Hughger/graduate/accelerator/pics/MCU200T.JPG

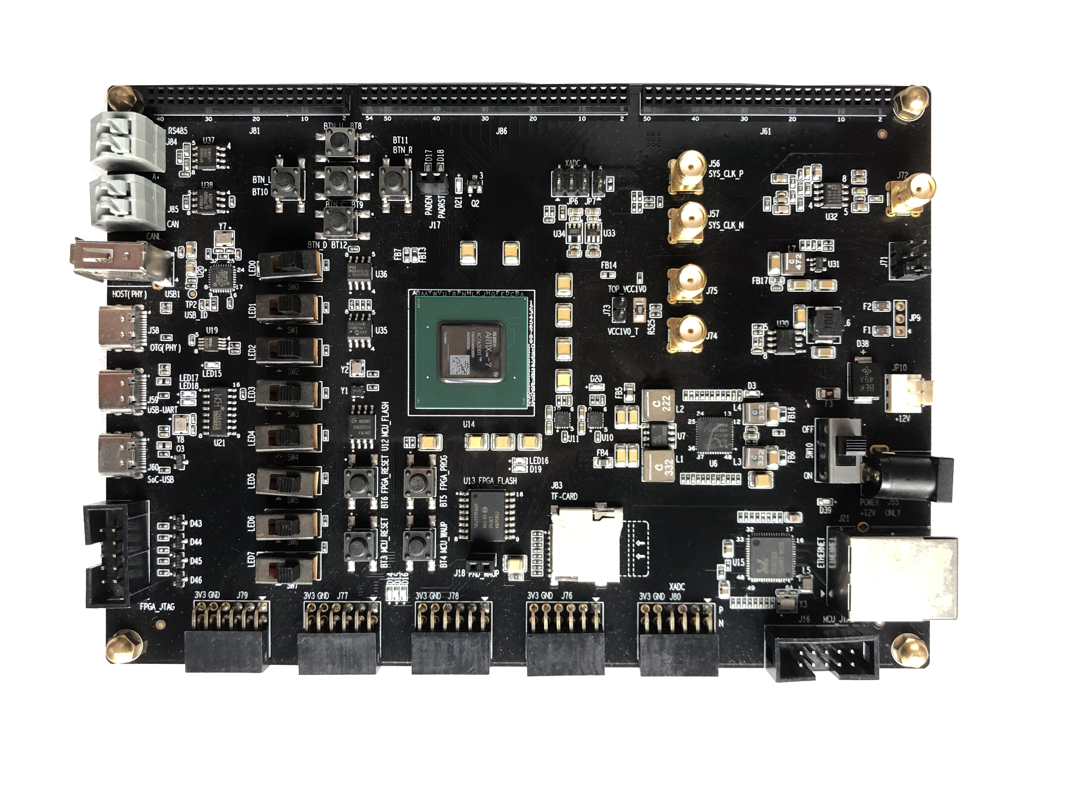
accelerator/pics/MCU200T.JPG
