Hughger/graduate/accelerator/note.md

# E203 RISC-V 处理器与 AHB 总线矩阵系统集成技术指南

## 目录
1.  [引言](#1-引言)
    1.1. [项目背景](#11-项目背景)
    1.2. [系统架构概述](#12-系统架构概述)
    1.3. [指南目标与范围](#13-指南目标与范围)
2.  [总线协议分析](#2-总线协议分析)
    2.1. [E203 内部 ICB 总线协议](#21-e203-内部-icb-总线协议)
        2.1.1. [ICB 总线信号详解](#211-icb-总线信号详解)
        2.1.2. [ICB 总线时序分析](#212-icb-总线时序分析)
    2.2. [AHB-Lite 与标准 AHB 协议](#22-ahb-lite-与标准-ahb-协议)
        2.2.1. [主要区别](#221-主要区别)
        2.2.2. [兼容性考量](#222-兼容性考量)
    2.3. [ICB 到 AHB-Lite 转换机制](#23-icb-到-ahb-lite-转换机制)
        2.3.1. [转换桥 (CIB2AHB) 的作用](#231-转换桥-cib2ahb-的作用)
        2.3.2. [信号匹配与转换逻辑](#232-信号匹配与转换逻辑)
        2.3.3. [被忽略或固定值的信号处理](#233-被忽略或固定值的信号处理)
3.  [代码级实现](#3-代码级实现)
    3.1. [关键源文件定位与修改](#31-关键源文件定位与修改)
        3.1.1. [E203 Core 相关文件](#311-e203-core-相关文件)
        3.1.2. [SoC 集成层面文件](#312-soc-集成层面文件)
        3.1.3. [总线矩阵配置文件](#313-总线矩阵配置文件)
    3.2. [地址空间分配](#32-地址空间分配)
        3.2.1. [系统地址映射规划](#321-系统地址映射规划)
        3.2.2. [E203 视角下的地址映射](#322-e203-视角下的地址映射)
        3.2.3. [修改地址译码逻辑](#323-修改地址译码逻辑)
    3.3. [在 AHB 矩阵中集成 E203 (作为主设备)](#33-在-ahb-矩阵中集成-e203-作为主设备)
        3.3.1. [AHB 主设备接口连接](#331-ahb-主设备接口连接)
        3.3.2. [总线矩阵仲裁配置](#332-总线矩阵仲裁配置)
    3.4. [AHB2APB 桥的连接与配置](#34-ahb2apb-桥的连接与配置)
        3.4.1. [APB 总线外设连接](#341-apb-总线外设连接)
        3.4.2. [配置寄存器访问 (regfile)](#342-配置寄存器访问-regfile)
    3.5. [最小化修改 E203 现有代码的策略](#35-最小化修改-e203-现有代码的策略)
4.  [集成挑战与解决方案](#4-集成挑战与解决方案)
    4.1. [多主设备环境下的总线仲裁](#41-多主设备环境下的总线仲裁)
    4.2. [地址映射与内存区域划分](#42-地址映射与内存区域划分)
    4.3. [数据宽度不匹配 (32位 E203 vs 64位 AHB/SRAM)](#43-数据宽度不匹配-32位-e203-vs-64位-ahbsram)
        4.3.1. [数据位宽转换逻辑](#431-数据位宽转换逻辑)
        4.3.2. [字节选通 (Byte Strobes) 处理](#432-字节选通-byte-strobes-处理)
    4.4. [时钟域同步](#44-时钟域同步)
        4.4.1. [CDC (Clock Domain Crossing) 设计](#441-cdc-clock-domain-crossing-设计)
        4.4.2. [异步 FIFO 的使用](#442-异步-fifo-的使用)
    4.5. [复位机制协调](#45-复位机制协调)
        4.5.1. [系统复位信号生成与分发](#451-系统复位信号生成与分发)
        4.5.2. [各模块复位序列](#452-各模块复位序列)
5.  [性能优化](#5-性能优化)
    5.1. [E203 访问内存的延迟分析与优化](#51-e203-访问内存的延迟分析与优化)
        5.1.1. [流水线与等待状态](#511-流水线与等待状态)
        5.1.2. [预取机制](#512-预取机制)
    5.2. [多主设备争用时的性能保障](#52-多主设备争用时的性能保障)
        5.2.1. [仲裁算法选择与调优](#521-仲裁算法选择与调优)
        5.2.2. [QoS (Quality of Service) 机制 (如果支持)](#522-qos-quality-of-service-机制-如果支持)
    5.3. [缓存策略调整建议 (E203 L1 Cache)](#53-缓存策略调整建议-e203-l1-cache)
6.  [调试与测试](#6-调试与测试)
    6.1. [总线信号监控点设置](#61-总线信号监控点设置)
        6.1.1. [关键信号列表](#611-关键信号列表)
        6.1.2. [ILA (Integrated Logic Analyzer) 使用](#612-ila-integrated-logic-analyzer-使用)
    6.2. [验证策略与测试用例设计](#62-验证策略与测试用例设计)
        6.2.1. [单元测试](#621-单元测试)
        6.2.2. [集成测试](#622-集成测试)
        6.2.3. [系统级测试](#623-系统级测试)
        6.2.4. [压力测试和边界条件测试](#624-压力测试和边界条件测试)
    6.3. [常见问题诊断与解决方法](#63-常见问题诊断与解决方法)
        6.3.1. [CPU 无法启动](#631-cpu-无法启动)
        6.3.2. [内存访问错误](#632-内存访问错误)
        6.3.3. [外设不工作](#633-外设不工作)
        6.3.4. [性能不达标](#634-性能不达标)
7.  [实现路线图](#7-实现路线图)
    7.1. [推荐的渐进式实现步骤](#71-推荐的渐进式实现步骤)
        7.1.1. [步骤一：基础 E203 系统搭建 (单主模式)](#711-步骤一基础-e203-系统搭建-单主模式)
        7.1.2. [步骤二：引入 AHB 总线矩阵和内存](#712-步骤二引入-ahb-总线矩阵和内存)
        7.1.3. [步骤三：集成 AHB2APB 桥和基础外设](#713-步骤三集成-ahb2apb-桥和基础外设)
        7.1.4. [步骤四：集成其他 AHB 主设备 (如 DMA, 网络接口)](#714-步骤四集成其他-ahb-主设备-如-dma-网络接口)
        7.1.5. [步骤五：集成 4x4 DSP 核心](#715-步骤五集成-4x4-dsp-核心)
    7.2. [关键验证点与里程碑](#72-关键验证点与里程碑)
    7.3. [最小可行产品 (MVP) 实现建议](#73-最小可行产品-mvp-实现建议)
8.  [附录](#8-附录)
    8.1. [相关术语解释](#81-相关术语解释)
    8.2. [参考资料](#82-参考资料)

## 1. 引言

### 1.1. 项目背景
随着物联网 (IoT)、嵌入式系统以及专用计算领域对高能效、可定制化处理器的需求日益增长，RISC-V 架构凭借其开放、模块化和可扩展的特性，受到了广泛关注。E203 是由芯来科技推出的一款基于 RISC-V RV32IMAC 指令集的低功耗、高性能嵌入式处理器核心。

在复杂的片上系统 (SoC) 设计中，处理器核心通常需要与多种内存、外设和加速器进行高效通信。AHB (Advanced High-performance Bus) 作为 AMBA (Advanced Microcontroller Bus Architecture) 总线规范的一部分，是连接这些组件的常用标准。本项目旨在将 E203 处理器集成到一个基于 AHB 总线矩阵的复杂系统中，该系统包含 DDR/SRAM 内存、网络接口、DMA 控制器以及一个专用的 4x4 DSP 计算核心，以满足特定应用场景下的数据处理和控制需求。

本指南将详细阐述集成过程中涉及的关键技术环节，旨在为初次接触此类项目的工程师提供清晰、详尽的操作指引。

### 1.2. 系统架构概述
根据提供的系统框图，我们集成的目标系统主要包含以下关键模块：

*   **E203 RISC-V 处理器**：作为系统的核心控制器，负责执行主程序逻辑。E203 处理器通过其内部的 ICB (Instruction and Data Coherent Bus) 总线（32位）与外界交互。
*   **CIB2AHB (ICB to AHB Bridge)**：这是一个关键的桥接模块，负责将 E203 的 32位 ICB 总线协议转换为 AHB-Lite 总线协议，使其能够连接到 AHB 总线矩阵。
*   **AHB 总线矩阵 (AHB Matrix)**：作为系统数据交换的枢纽，连接了多个主设备 (Master) 和从设备 (Slave)。
    *   **主设备 (Masters)** 包括：
        *   E203 处理器 (通过 CIB2AHB，32位接口)
        *   三个 DMA 控制器 (DMA0, DMA1, DMA2，预计为64位接口)
        *   网络接口或其他高速外设 (预计为64位接口)
    *   **从设备 (Slaves)** 包括：
        *   DDR/SRAM 内存控制器 (64位接口)
        *   AHB2APB 桥 (为 E203 提供访问低速外设的通道，如配置寄存器)
        *   DMA 控制器的从接口 (用于接收来自 AHB Matrix 的数据传输指令或状态查询)
*   **DDR/SRAM 内存**：系统主内存，通过 64位接口连接到 AHB 总线矩阵，供 E203 和其他主设备访问。
*   **网络接口/其他外设**：作为 AHB 主设备，通过 64位接口与系统其他部分进行数据交换。
*   **4x4 DSP 核心**：专用的数字信号处理单元，不直接挂载在 AHB 总线矩阵上。它通过三个专用的 SRAM (sram0 用于输入，sram1 用于权重，sram2 用于输出) 与系统交互。
    *   DMA0 负责将输入数据从系统内存（如 DDR/SRAM）搬运到 `sram0` (64位 -> 512位路径)。
    *   DMA1 负责将权重数据搬运到 `sram1` (64位 -> 512位路径)。
    *   `sram0` 和 `sram1` 的数据提供给 4x4 DSP 核心进行计算。
    *   DSP 核心的计算结果存入 `sram2` (512位)。
    *   DMA2 负责将 `sram2` 中的输出数据搬运回系统内存 (512位 -> 64位路径)。
*   **AHB2APB 桥 (AHB to APB Bridge)**：连接到 AHB 总线矩阵，并将 AHB 事务转换为 APB (Advanced Peripheral Bus) 事务。APB 总线通常用于连接低带宽、低功耗的外设，如本系统中的**配置寄存器**。E203 通过此桥来配置和控制这些外设。
*   **数据位宽**：系统存在多种数据位宽：
    *   E203 CPU 核及 CIB2AHB 输出为 32 位。
    *   AHB 矩阵的大部分高速接口（DDR/SRAM, DMA, 网络接口）为 64 位。
    *   DSP 核相关的 SRAM 接口为 512 位。
    *   AHB2APB 桥的 AHB 侧通常与 CPU 位宽匹配 (32位)，APB 侧位宽根据外设需求而定。

理解这些模块及其交互方式是成功集成的第一步。

### 1.3. 指南目标与范围
本指南的目标是为用户提供一个全面、细致的集成方案，涵盖从理论分析到具体实践的各个方面。主要内容包括：

*   **深入的总线协议理解**：解析 E203 的 ICB 总线、AHB-Lite 与标准 AHB 的差异，以及 ICB 到 AHB-Lite 的转换细节。
*   **详细的代码级实现指导**：指出需要修改的关键源文件、地址空间的配置方法、E203 在 AHB 矩阵中的集成方式以及 AHB2APB 桥的连接。
*   **清晰的集成挑战剖析**：讨论多主仲裁、地址映射、数据宽度不匹配、时钟域同步和复位协调等常见难题及应对策略。
*   **实用的性能优化建议**：针对内存访问延迟、总线争用和缓存利用提出优化方案。
*   **系统的调试与测试方法**：提供总线监控、验证策略和问题排查的思路。
*   **明确的实现路线图**：给出分步实施计划、关键验证节点和 MVP (Minimum Viable Product) 建议。

本指南力求做到：
*   **逻辑清晰**：确保内容的组织结构合理，易于理解。
*   **深度与形象并存**：在保证技术深度的同时，采用生动的描述和必要的图示（尽管本文档主要为文本）来帮助理解。
*   **细节充分**：提供足够的代码示例（概念性或通用性）、配置参数和修改建议。

**范围限制**：
*   本指南主要关注 E203 处理器与 AHB 总线系统的集成。对于特定外设（如 DDR 控制器、网络接口、DSP 核）的内部详细设计和驱动开发，将不作深入探讨，仅涉及其与总线接口相关的部分。
*   提供的代码示例将主要基于通用 Verilog/SystemVerilog 描述，具体实现可能需要根据用户实际使用的 E203 版本和 SoC 开发环境进行调整。
*   本指南假设用户具备基础的数字逻辑设计、Verilog/SystemVerilog 语言以及嵌入式系统概念的知识。

希望通过本指南，即使是刚接触此项目的工程师也能对集成过程有一个清晰的认识，并能够按部就班地完成各项任务。

## 2. 总线协议分析

理解系统中涉及的各种总线协议是成功集成的基石。本章节将重点分析 E203 处理器的内部总线 (ICB)、目标系统总线 (AHB-Lite/AHB) 以及它们之间的转换机制。

### 2.1. E203 内部 ICB 总线协议
E203 处理器核（如本项目中的 e203_hbirdv2）使用一种称为 ICB (Internal Chip Bus) 的内部总线接口。这是一种同步总线协议，用于连接处理器核的指令获取单元 (IFU) 和加载存储单元 (LSU) 到外部总线桥 (如 CIB2AHB，连接到 AHB 系统总线) 或紧耦合内存 (TCM)。ICB 通常具有分离的命令和响应通道，并使用 `valid/ready` 握手机制。

该项目的 RTL 代码中，通过 `rtl/e203/core/e203_ifu_ift2icb.v` 文件可以了解到 IFU 侧的 ICB 接口信号，通过 `rtl/e203/core/e203_lsu.v`、`rtl/e203/core/e203_biu.v` 等文件可以明确 LSU 侧的 ICB 接口信号。相关信号的位宽则由 `rtl/e203/core/e203_defines.v` (及其包含的 `config.v`) 文件确定。

#### 2.1.1. ICB 总线信号详解
E203 的 ICB 接口分为指令端 (IFU) 和数据端 (LSU)。以下是基于对 `e203_hbirdv2` RTL 核心代码的分析所确认的信号描述。

**通用 ICB 信号特性:**
*   所有 ICB 信号均同步于处理器的核心时钟。
*   使用 `valid/ready` 握手协议。
*   命令通道 (`_cmd_`) 和响应通道 (`_rsp_`) 通常是分离的。

**1. 指令获取单元 (IFU) 的 ICB 主接口 (例如，连接到 BIU 的前缀为 `ifu2biu_icb_`，连接到 ITCM 的前缀为 `ifu2itcm_icb_`)**
   IFU 主要发起读请求以获取指令，因此其 ICB 接口主要涉及读操作。

*   **请求通道 (IFU -> BIU/ITCM)**
    *   `ifu_icb_cmd_valid`: 1位输出，命令有效。表示 IFU 发出一个有效的指令读取请求。
    *   `ifu_icb_cmd_addr`: [`E203_ADDR_SIZE-1:0`] 输出，请求的指令地址。位宽由 `E203_ADDR_SIZE` (例如32位) 决定。
    *   `ifu_icb_cmd_read`: 1位输出，恒为1，表示读请求。(在 `e203_biu.v` 中，`ifu2biu_icb_cmd_read` 信号存在且被使用)
    *   `ifu_icb_cmd_burst`: 2位输出 (例如在 `ifu2biu_icb_cmd_burst`)，突发类型 (如 `INC4`, `SINGLE`)。
    *   `ifu_icb_cmd_beat`: 2位输出 (例如在 `ifu2biu_icb_cmd_beat`)，突发拍数。
    *   `ifu_icb_cmd_lock`: 1位输出 (例如在 `ifu2biu_icb_cmd_lock`)，指示锁定传输 (通常对 IFU 为低)。
    *   `ifu_icb_cmd_excl`: 1位输出 (例如在 `ifu2biu_icb_cmd_excl`)，指示独占访问 (通常对 IFU 为低)。
    *   `ifu_icb_cmd_size`: 2位输出 (例如在 `ifu2biu_icb_cmd_size`)，传输大小 (例如字节、半字、字)。

*   **命令响应通道 (BIU/ITCM -> IFU)**
    *   `ifu_icb_cmd_ready`: 1位输入，命令准备好。表示总线桥或 ITCM 可以接收 IFU 的新请求。

*   **读数据响应通道 (BIU/ITCM -> IFU)**
    *   `ifu_icb_rsp_valid`: 1位输入，响应有效。表示总线桥或 ITCM 返回了有效的指令数据或错误指示。
    *   `ifu_icb_rsp_rdata`: [`E203_SYSMEM_DATA_WIDTH-1:0`] 或 [`E203_ITCM_DATA_WIDTH-1:0`] 输入，读取到的指令数据。位宽取决于目标：
        *   系统内存 (BIU): `E203_SYSMEM_DATA_WIDTH` (例如32位或64位)。
        *   ITCM: `E203_ITCM_DATA_WIDTH` (例如64位)。
    *   `ifu_icb_rsp_err`: 1位输入，响应错误。表示指令读取过程中发生错误。
    *   `ifu_icb_rsp_excl_ok`: 1位输入 (例如在 `ifu2biu_icb_rsp_excl_ok`)，独占访问成功 (通常对 IFU 为低)。
    *   `ifu_icb_rsp_ready`: 1位输出，响应准备好。表示 IFU 可以接收响应数据/错误。

**2. 加载存储单元 (LSU) 的 ICB 主接口 (例如，连接到 BIU 的前缀为 `lsu2biu_icb_`，连接到 DTCM 的前缀为 `lsu2dtcm_icb_`)**
   LSU 发起读写请求以访问数据内存。其信号集比 IFU 更完整，支持写操作、字节使能、独占访问等。

*   **请求通道 (LSU -> BIU/DTCM)**
    *   `lsu_icb_cmd_valid`: 1位输出，命令有效。
    *   `lsu_icb_cmd_addr`: [`E203_ADDR_SIZE-1:0`] 输出，访问地址。
    *   `lsu_icb_cmd_read`: 1位输出，读写指示。高电平表示读，低电平表示写。
    *   `lsu_icb_cmd_wdata`: [`E203_XLEN-1:0`] 输出，写数据。CPU 内核数据宽度 `E203_XLEN` 通常为32位。
    *   `lsu_icb_cmd_wmask`: [`E203_XLEN/8-1:0`] 输出，写操作字节使能。对于32位 `E203_XLEN`，此宽度为4位 (例如 `0b0001` 写低字节, `0b1111` 写整个字)。
    *   `lsu_icb_cmd_lock`: 1位输出，锁定传输信号。用于原子操作或连续不可中断的访问。
    *   `lsu_icb_cmd_excl`: 1位输出，独占访问请求。用于 Load-Reserved/Store-Conditional (LR/SC) 指令。
    *   `lsu_icb_cmd_size`: 2位输出，传输大小。编码方式通常为 `00`: 字节, `01`: 半字, `10`: 字。
    *   `lsu_icb_cmd_burst`: (可选，但在 `lsu2biu_icb_` 接口中存在) 2位输出，突发类型。
    *   `lsu_icb_cmd_beat`: (可选，但在 `lsu2biu_icb_` 接口中存在) 2位输出，突发拍数。
    *   `lsu_icb_cmd_amo`: RISC-V 'A' 扩展中的原子内存操作并非通过一个名为 `lsu_icb_cmd_amo` 的专用多位ICB信号直接指示其类型。其功能主要通过 `lsu_icb_cmd_excl` (用于LR/SC) 和常规的读写操作，结合LSU内部逻辑 (如 `e203_lsu.v` 中的 `lsu_req_amo` 信号输入给LSU控制逻辑) 来实现。

*   **命令响应通道 (BIU/DTCM -> LSU)**
    *   `lsu_icb_cmd_ready`: 1位输入，命令准备好。

*   **读数据/写响应通道 (BIU/DTCM -> LSU)**
    *   `lsu_icb_rsp_valid`: 1位输入，响应有效。
    *   `lsu_icb_rsp_rdata`: [`E203_SYSMEM_DATA_WIDTH-1:0`] 或 [`E203_DTCM_DATA_WIDTH-1:0`] 输入，读数据。位宽取决于目标：
        *   系统内存 (BIU): `E203_SYSMEM_DATA_WIDTH` (例如32位或64位)。
        *   DTCM: `E203_DTCM_DATA_WIDTH` (例如32位)。
    *   `lsu_icb_rsp_err`: 1位输入，响应错误。例如，总线错误 (slave error) 或独占访问失败。
    *   `lsu_icb_rsp_excl_ok`: 1位输入，独占访问成功响应。对于 SC 指令，此信号高表示原子写操作成功。
    *   `lsu_icb_rsp_ready`: 1位输出，响应准备好。LSU 准备好接收读数据或写响应。

**关键特性总结 (基于对 `e203_hbirdv2` RTL 的分析):**
*   **分离的指令和数据接口**: E203 核的 IFU 和 LSU 分别通过独立的 ICB 接口连接到总线接口单元 (BIU) 或直接连接到 TCM。BIU 内部会将这些请求仲裁并转发到外部总线 (如 AHB)。
*   **握手协议**: `valid/ready` 机制确保命令和响应的可靠传输。
*   **支持原子操作**: LSU 的 ICB 接口通过 `_cmd_excl` 和 `_rsp_excl_ok` 支持 RISC-V 的 Load-Reserved/Store-Conditional (LR/SC) 指令，这是实现原子操作的基础。对于其他的 AMO 指令 (如 AMOSWAP, AMOADD 等)，LSU 内部 (`e203_exu_alu_lsuagu.v` 解码生成 `agu_i_amo*` 信号, 传递给 `e203_lsu.v` 的 `lsu_req_amo*` 输入) 会将这些操作分解为一个或多个 ICB 读和/或写事务，配合 `_cmd_lock` (如果需要确保操作的原子性不被外部总线仲裁打断) 或 `_cmd_excl` (对于 LR/SC 序列) 来完成。LSU 对外的 ICB 接口上并没有一个专门的 `lsu_icb_cmd_amo` 多位信号来直接传递 AMO 操作的类型。
*   **支持不同传输大小**: `_cmd_size` 信号允许字节、半字和字访问。
*   **突发传输能力**: IFU 和 LSU 到 BIU 的 ICB 接口均包含 `_cmd_burst` 和 `_cmd_beat` 信号，表明 ICB 支持突发传输，这对于提高数据传输效率非常重要。

#### 2.1.2. ICB 总线时序分析
ICB 总线是一种同步总线，所有信号都相对于同一个时钟沿进行采样和驱动。

*   **读操作时序 (简例，以LSU为例)**：
    1.  **T1周期**：LSU 主设备拉高 `lsu_icb_cmd_valid`，并驱动 `lsu_icb_cmd_addr` (读地址) 和 `lsu_icb_cmd_read` (高电平)。
    2.  总线桥/从设备在同一周期或稍后周期拉高 `lsu_icb_cmd_ready` (如果能立即接收)。命令被锁存。
    3.  经过若干周期（取决于从设备延迟），总线桥/从设备准备好读数据。
    4.  **Tn周期**：总线桥/从设备拉高 `lsu_icb_rsp_valid`，并驱动 `lsu_icb_rsp_rdata` (读出的数据) 和 `lsu_icb_rsp_err` (若有错误)。LSU 此时拉高 `lsu_icb_rsp_ready` (通常 LSU 会一直拉高 `rsp_ready` 表示能接收) 接收响应。

*   **写操作时序 (简例，以LSU为例)**：
    1.  **T1周期**：LSU 主设备拉高 `lsu_icb_cmd_valid`，并驱动 `lsu_icb_cmd_addr` (写地址)，`lsu_icb_cmd_read` (低电平)，`lsu_icb_cmd_wdata` (写数据) 和 `lsu_icb_cmd_wmask`。
    2.  总线桥/从设备在同一周期或稍后周期拉高 `lsu_icb_cmd_ready`。命令和数据被锁存。
    3.  经过若干周期，写操作完成。
    4.  **Tm周期**：总线桥/从设备拉高 `lsu_icb_rsp_valid` (指示写完成) 和 `lsu_icb_rsp_err` (若有错误)。LSU 接收写响应。

**关键时序考量**：
*   **延迟 (Latency)**：从命令发出到接收到响应（读数据或写完成）的时钟周期数。
*   **吞吐率 (Throughput)**：单位时间内可以传输的数据量。ICB 的设计允许一定程度的流水线操作，即在等待前一个命令的响应时，可以发出新的命令 (如果 `icb_cmd_ready` 允许)。

### 2.2. AHB-Lite 与标准 AHB 协议
AMBA AHB (Advanced High-performance Bus) 是一种广泛使用的高性能片上总线协议。AHB-Lite 是 AHB 的一个子集，专为单个主设备系统或不需复杂仲裁和不支持分离事务的场景设计，但它也可以作为多主系统中连接简单主设备或通过桥接转换后的主设备接口。

#### 2.2.1. 主要区别
下表总结了 AHB-Lite 与标准 AHB (例如 AHB5，但也适用于早期版本如 AHB2) 的一些主要区别：

| 特性 | 标准 AHB (Full AHB) | AHB-Lite |
| --- | --- | --- |
| **主设备数量** | 支持多个主设备 (Multi-Master) | 通常用于单个主设备，或多主系统中简单主设备接口 |
| **仲裁** | 需要中央仲裁器 (Arbiter) | 无内置仲裁逻辑 (假定只有一个主设备，或由外部处理) |
| **分离事务** | 支持 (Split Transactions) | 不支持 |
| **流水线深度** | 通常支持更深的流水线 | 流水线相对简单 |
| **RETRY响应** | 支持 | 不支持 (通常 slave 用 HREADY 拉长传输) |
| **保护信号** | `HPROT` 提供更丰富的保护信息 | `HPROT` 可能被简化或固定 |
| **锁定传输** | `HLOCKx` 支持精确的锁定序列 | `HLOCKx` 通常用于简单的锁定传输 |
| **突发操作** | 支持多种复杂的突发类型 (e.g., WRAP4/8/16, INCR4/8/16) | 支持基本的 INCR 和 SINGLE 突发类型 |
| **信号数量** | 信号较多 | 信号较少 |

在我们的系统中，E203 通过 CIB2AHB 桥连接到 AHB 总线矩阵。这意味着 CIB2AHB 模块的输出是 AHB-Lite 兼容的接口，而 AHB 总线矩阵本身则需要处理来自多个主设备（包括转换后的 E203）的请求，因此总线矩阵必须实现仲裁逻辑，表现得像一个标准 AHB 系统中的互联结构。

#### 2.2.2. 兼容性考量
*   **AHB-Lite 主设备到标准 AHB 从设备**：通常是兼容的。AHB-Lite 主设备发出的事务可以被标准 AHB 从设备理解和处理。从设备通过 `HREADY` 信号来控制传输的完成，通过 `HRESP` 来指示成功或错误。
*   **AHB-Lite 主设备到 AHB 总线矩阵**：CIB2AHB 产生的 AHB-Lite 信号作为主设备接口连接到 AHB 总线矩阵的一个主端口。总线矩阵负责将来自 E203 (以及其他主设备) 的请求路由到相应的从设备，并处理仲裁。
*   **关键信号**：对于 AHB-Lite 主设备，核心信号包括：
    *   `HCLK`: 总线时钟
    *   `HRESETn`: 总线复位 (低有效)
    *   `HADDR[31:0]`: 地址总线
    *   `HWDATA[31:0]`: 写数据总线 (对于32位系统)
    *   `HRDATA[31:0]`: 读数据总线 (对于32位系统)
    *   `HWRITE`: 传输方向 (高=写, 低=读)
    *   `HSIZE[2:0]`: 传输大小 (字节,半字,字)
    *   `HBURST[2:0]`: 突发类型 (SINGLE, INCR, WRAP4, INCR4, etc.)
    *   `HPROT[3:0]`: 保护控制 (指令/数据, 用户/特权, 可缓冲, 可缓存)
    *   `HTRANS[1:0]`: 传输类型 (IDLE, BUSY, NONSEQ, SEQ)
    *   `HMASTLOCK`: 主设备锁定总线
    *   `HSELx`: 从设备选择信号 (由总线矩阵或地址译码器产生，送给从设备)
    *   `HREADY`: 从设备或总线准备好信号 (输入到主设备)。高表示传输完成，低表示等待。
    *   `HRESP`: 从设备响应 (OKAY, ERROR)

### 2.3. ICB 到 AHB-Lite 转换机制
CIB2AHB (ICB to AHB Bridge) 模块是实现 E203 处理器与 AHB 总线系统对接的关键。它扮演着协议转换器的角色。

#### 2.3.1. 转换桥 (CIB2AHB) 的作用
CIB2AHB 模块的主要职责是将 E203 CPU 核发出的 ICB 总线事务（读/写请求）转换为标准的 AHB-Lite 总线事务，并将 AHB 从设备返回的响应（读数据、错误状态）转换回 ICB 总线的响应格式。

具体功能包括：
1.  **地址和控制信号映射**：将 ICB 的地址、读写控制、字节使能等信号转换为 AHB 的 `HADDR`, `HWRITE`, `HSIZE`, `HWDATA` (部分字节由 `icb_cmd_wmask` 控制) 等。
2.  **时序匹配**：ICB 通常是 `valid/ready` 握手，AHB 也有其两阶段（地址相、数据相）和 `HREADY` 控制的握手机制。桥需要正确处理这些时序关系。
3.  **响应转换**：将 AHB 的 `HRDATA`, `HRESP` 转换为 ICB 的 `icb_rsp_rdata`, `icb_rsp_err`。
4.  **错误处理**：将 AHB 总线错误 (`HRESP`=ERROR) 传递回 ICB 总线。
5.  **等待状态插入**：如果 AHB 从设备通过拉低 `HREADY` 来请求等待状态，CIB2AHB 桥需要相应地暂停对 E203 ICB 总线的 `icb_cmd_ready` (如果 CPU 正在等待上一个命令完成才能发下一个) 或/和 `icb_rsp_valid`。

#### 2.3.2. 信号匹配与转换逻辑 (示例性，基于更新的 ICB 信号知识)
以下是一些典型的信号映射关系 (重点关注 LSU 的 D-ICB，因为它更完整):

*   **ICB Command (CPU LSU -> Bridge) to AHB (Bridge -> Matrix/Slave)**:
    *   `lsu_icb_cmd_addr`[`E203_ADDR_SIZE-1:0`] -> `HADDR`[`E203_ADDR_SIZE-1:0`] (或根据系统AHB总线宽度调整，通常CPU地址总线宽度与AHB地址总线宽度一致，均为32位)
    *   `lsu_icb_cmd_read` (1 for read, 0 for write) -> `HWRITE` (0 for read, 1 for write) (注意逻辑反转)
    *   `lsu_icb_cmd_wdata`[`E203_XLEN-1:0`] -> `HWDATA`[`E203_XLEN-1:0`] (在写操作时，通常 E203_XLEN 是32位，对应32位 AHB 数据总线)
    *   `lsu_icb_cmd_wmask`[`E203_XLEN/8-1:0`] -> 转换为 AHB 的 `HSIZE`。AHB-Lite 本身不直接使用字节选通信号 `HSTRB` (那是 AXI 的特性)。`HSIZE` 结合地址的低两位来确定传输的字节、半字或字。CIB2AHB 桥需要根据 `lsu_icb_cmd_wmask` 和 `lsu_icb_cmd_addr`的低位来生成正确的 `HSIZE` 和 `HADDR`。例如：
        *   写字节 (e.g., `4'b0001` at addr `0x0`): `HSIZE=000` (byte), `HADDR[1:0]=00`
        *   写半字 (e.g., `4'b0011` at addr `0x0`): `HSIZE=001` (halfword), `HADDR[1:0]=00`
        *   写字 (e.g., `4'b1111` at addr `0x0`): `HSIZE=010` (word), `HADDR[1:0]=00`
        如果 ICB 发出的是对齐的32位访问 (`wmask=4'b1111`)，则 `HSIZE` 通常设为 `3'b010` (32-bit word)。对于部分写 (如 `sb`, `sh`)，桥需要正确设置 `HSIZE` 并确保 `HADDR` 对齐到 `HSIZE` 的边界，同时 `HWDATA` 中只有对应的字节/半字数据是有效的（其他字节可以是不定值，从设备应忽略）。
    *   `lsu_icb_cmd_valid` -> 触发 AHB 传输的开始 (`HTRANS` 从 IDLE 变为 NONSEQ/SEQ)。
    *   `lsu_icb_cmd_ready` (from Bridge to CPU) -> 当桥的 AHB 侧可以发起新传输或已完成当前传输的地址阶段时，可以拉高 `lsu_icb_cmd_ready`。

*   **AHB Response (Matrix/Slave -> Bridge) to ICB Response (Bridge -> CPU LSU)**:
    *   `HRDATA`[`E203_XLEN-1:0`] (假设AHB数据总线与CPU XLEN一致) -> `lsu_icb_rsp_rdata`[`E203_XLEN-1:0`] (在读操作响应时)
    *   `HRESP` (OKAY/ERROR) -> `lsu_icb_rsp_err` (ERROR 时 `lsu_icb_rsp_err` 为高)
    *   `HREADY` (high indicates data phase completion) -> 触发 `lsu_icb_rsp_valid` 的产生。

**事务状态机**: CIB2AHB 内部会有一个状态机来管理 ICB 请求到 AHB 事务的转换过程，包括 AHB 的地址阶段和数据阶段，以及处理 `HREADY` 引入的等待周期。

**突发传输 (Burst)**：
*   如果 ICB 接口 (`lsu_icb_cmd_burst`, `lsu_icb_cmd_beat`) 支持突发，CIB2AHB 桥需要将这些转换为 AHB 的 `HBURST` 和管理多拍 (`HTRANS` 为 SEQ)。
*   如果 E203 配置了指令缓存 (I-Cache) 或数据缓存 (D-Cache)（通过如 `E203_HAS_ICACHE`/`E203_HAS_DCACHE` 等宏配置），其缓存行（Cache line）的填充 (fill) 或写回 (write-back) 操作会在 ICB 层面产生突发请求，利用 `ifu2biu_icb_cmd_burst`/`beat` 或 `lsu2biu_icb_cmd_burst`/`beat` 信号。标准的 RISC-V 指令集不包含 LDM/STM (加载/存储多寄存器) 指令，E203 的公开资料和代码中也未明确提及此类自定义指令。
*   如果 ICB 不直接支持突发，但 CPU 连续发出地址相邻的请求，桥也可以选择将它们合并成一个 AHB 突发（需要更复杂的逻辑）。更常见的是，CPU的加载/存储多寄存器指令或 Cache 操作会触发桥产生固定长度的 AHB 突发。

#### 2.3.3. 被忽略或固定值的信号处理
在 ICB 到 AHB-Lite 的转换中，某些 AHB 信号可能对于简单的 E203 应用场景不是必需的，或者其值可以固定：

*   **`HMASTLOCK`**: 如果 E203 的 `lsu_icb_cmd_lock` 被驱动，则桥应相应驱动 `HMASTLOCK`。
*   **`HPROT` (Protection Control)**: ICB 的 `lsu_icb_cmd_prot` (如果存在) 可以部分映射到 `HPROT`。CIB2AHB 需要根据 E203 的内存访问类型（指令取指、数据加载/存储，通过是I-ICB还是D-ICB判断）以及当前的运行模式（用户态/特权态，这部分信息需要 CIB2AHB 桥根据 E203 的当前状态和访问特性来生成。具体来说：CPU 的当前特权级别（用户态/机器态，可从 CSR如 `mstatus` 获取）会影响 `HPROT[1]` (user/privilege)；访问的内存区域属性（是否可缓存、可缓冲，由 PMP 单元或地址区域的默认设定决定）会影响 `HPROT[3]` (cacheable) 和 `HPROT[2]` (bufferable)；访问是取指还是数据访问会影响 `HPROT[0]` (instruction/data)。PMP 单元会检查访问权限，但具体的属性信息（用于 `HPROT\`）如何从 PMP 传递给桥，取决于桥和 PMP 的接口设计，或桥通过地址范围和操作类型推断。)来设置这些位。
*   **`HBURST`**: 根据 `lsu_icb_cmd_burst` (如果存在) 或固定为 SINGLE/INCR。
*   **`HSIZE`**: 根据 `lsu_icb_cmd_wmask` 和地址低位计算，或对于IFU固定为适合指令获取的宽度（通常是字）。

理解这些协议细节和转换机制，对于后续的 RTL 代码修改、地址映射配置以及系统调试至关重要。

## 3. 代码级实现

本章节将指导您如何在 RTL (Register Transfer Level) 代码层面进行 E203 处理器与 AHB 总线矩阵系统的集成。这通常涉及到修改现有的 SoC 顶层文件、总线桥接逻辑、以及可能的处理器配置。

**重要提示**：以下提供的路径和文件名是基于典型 E203 项目结构和通用 SoC 设计实践的推测。您需要根据您项目中 `e203_hbirdv2` 代码库的实际结构来定位和修改相应文件。

### 3.1. 关键源文件定位与修改

#### 3.1.1. E203 Core 相关文件
*   **确切路径**: `rtl/e203/core/` （本项目已确认）
*   **关注点**: 通常情况下，E203 处理器核本身（如 `e203_cpu_top.v` 或类似文件）的 ICB 接口是标准化的，**不建议直接修改处理器核内部代码**，除非有非常特殊且明确的需求（例如，调整内部 TCM 大小或接口特性，但这通常通过顶层参数配置实现）。
*   **主要操作**: 理解 E203 核的 ICB 主端口（指令和数据）的信号列表和时序特性。这些信息通常在处理器核的顶层模块定义中可以找到，或者在其相关的接口定义文件（如 `e203_defines.v` 或 `e203_icb_if.vh` 等，如果存在的话）。

#### 3.1.2. CIB2AHB (ICB to AHB Bridge) 模块
*   **确切文件**: `rtl/e203/general/sirv_gnrl_icbs.v` 中的模块 `sirv_gnrl_icb2ahbl`（行号 1467 起）。该模块已完整实现 32-bit ICB → AHB-Lite 转换，无需再编写新桥。
*   **关注点**: 这是集成的核心模块之一。
    *   **参数配置**: 检查该桥模块是否有可配置的参数，例如 AHB 数据位宽（虽然图示中 E203 侧是32位，但桥的 AHB 输出也是32位）、地址位宽、是否支持某些 AHB 特性（如锁定传输）。
    *   **ICB 接口连接**: 确保 E203 处理器的指令 ICB (I-ICB) 和数据 ICB (D-ICB) 正确连接到此桥的对应 ICB 从端口。
        *   E203 通常有独立的指令获取接口和数据访问接口。这两个接口可能连接到同一个 CIB2AHB 模块（如果桥内部有仲裁能力和端口合并），或者分别连接到不同的总线路径或桥模块。根据系统图，E203 通过一个 CIB2AHB 连接到 AHB Matrix，这意味着指令和数据请求都通过这个桥。
    *   **AHB 主接口信号**: 桥模块输出的 AHB 主接口信号（`HADDR`, `HWDATA`, `HWRITE`, `HTRANS`, `HSIZE`, `HBURST`, `HPROT`, `HMASTLOCK` 等）需要被引出，并连接到 AHB 总线矩阵的主端口。
    *   **AHB 从响应信号**: 从 AHB 总线矩阵返回的响应信号（`HRDATA`, `HREADYIN` (来自被选中从设备的HREADY), `HRESP`）需要正确输入到桥模块。
*   **修改示例 (概念性 Verilog 片段 - 模块实例化)**:
    ```verilog
    // 在 SoC 顶层或子系统中实例化 CIB2AHB 桥
    // (假设 E203 的指令和数据 ICB 合并或通过同一桥访问)
    wire [31:0] e203_icb_cmd_addr;
    wire        e203_icb_cmd_valid;
    // ... 其他 E203 ICB 信号 ...
    wire [31:0] ahb_master_haddr;
    wire        ahb_master_hwrite;
    // ... 其他桥输出的 AHB 主接口信号 ...
    wire [31:0] ahb_slave_hrdata;
    wire        ahb_slave_hready;
    // ... 其他桥输入的 AHB 从响应信号 ...

    cib2ahb_bridge_wrapper u_cib2ahb_bridge (
        // ICB Slave Interface (Connected to E203 Master Ports)
        .i_icb_cmd_valid    (e203_icb_cmd_valid),
        .i_icb_cmd_addr     (e203_icb_cmd_addr),
        .i_icb_cmd_read     (e203_icb_cmd_read),
        .i_icb_cmd_wdata    (e203_icb_cmd_wdata),
        .i_icb_cmd_wmask    (e203_icb_cmd_wmask),
        .o_icb_cmd_ready    (e203_icb_cmd_ready),
        .o_icb_rsp_valid    (e203_icb_rsp_valid),
        .o_icb_rsp_rdata    (e203_icb_rsp_rdata),
        .o_icb_rsp_err      (e203_icb_rsp_err),
        .i_icb_rsp_ready    (1'b1), // Assuming CPU always accepts response

        // AHB Master Interface (Connected to AHB Matrix Master Port)
        .o_HADDR            (ahb_master_haddr),
        .o_HWRITE           (ahb_master_hwrite),
        .o_HTRANS           (ahb_master_htrans),
        // ... 其他 AHB 输出 ...
        .i_HRDATA           (ahb_slave_hrdata),
        .i_HREADY           (ahb_slave_hready_from_matrix),
        .i_HRESP            (ahb_slave_hresp_from_matrix),

        // Clock and Reset
        .i_HCLK             (hclk),
        .i_HRESETn          (hresetn)
    );
    ```

#### 3.1.3. AHB 总线矩阵 (Interconnect Fabric)
*   **当前代码库未包含 AHB Matrix**。请引入第三方 AHB-Lite Matrix/IP（如 Synopsys DW_ahb、ARM AHB5 Matrix，或开源 *ahb-lite-xbar*），并在 SoC 顶层实例化。
*   **关注点**:
    *   **主端口 (Master Ports)**: 需要为 CIB2AHB 模块（代表 E203）分配一个 AHB 主端口。如果矩阵是可配置的（例如通过参数指定主从设备数量），确保参数设置正确。
    *   **从端口 (Slave Ports)**: 需要为所有 AHB 从设备（DDR/SRAM 控制器, DMA 控制器的从接口, 网络接口的从接口, AHB2APB 桥）分配 AHB 从端口。
    *   **连接性**: 将 CIB2AHB 的 AHB 主接口连接到矩阵的一个主端口。将所有 AHB 从设备的接口连接到矩阵的从端口。
    *   **仲裁逻辑**: 矩阵内部包含仲裁器。需要理解或配置其仲裁策略（如固定优先级、轮询等）。E203 作为通用处理器，通常应具有较高的优先级，但需根据系统需求平衡。
    *   **地址译码**: 矩阵内部或外部（连接到矩阵从端口选择信号）需要地址译码逻辑，以根据 `HADDR` 将主设备的请求路由到正确的从设备。
*   **修改示例 (概念性 - 矩阵实例化和连接)**:
    ```verilog
    // 在 SoC 顶层实例化 AHB 总线矩阵
    // 假设矩阵有 M_MASTERS 个主端口和 S_SLAVES 个从端口
    ahb_matrix #(
        .NUM_MASTERS(M_MASTERS), // e.g., E203, DMA0, DMA1, DMA2, NET_IF
        .NUM_SLAVES (S_SLAVES)  // e.g., DDR_SRAM, AHB2APB, DMA_SLAVE_PORTS
    ) u_ahb_matrix (
        .HCLK      (hclk),
        .HRESETn   (hresetn),

        // Master Ports connections
        // Port 0: E203 (via CIB2AHB)
        .master_if_awaddr[0]    (ahb_master_haddr_from_cib), // HADDR
        .master_if_wdata[0]    (ahb_master_hwdata_from_cib),
        // ... other master signals from CIB2AHB ...
        .master_if_rdata[0]    (ahb_slave_hrdata_to_cib),
        .master_if_ready[0]    (ahb_slave_hready_to_cib), // HREADYOUT from slave
        .master_if_resp[0]     (ahb_slave_hresp_to_cib),

        // Port 1: DMA0
        // ... DMA0 AHB master signals ...

        // ... other master ports ...

        // Slave Ports connections
        // Port 0: DDR/SRAM Controller
        .slave_if_awaddr[0]    (haddr_to_ddr_sram),
        // ... other slave signals to/from DDR/SRAM ...

        // Port 1: AHB2APB Bridge
        .slave_if_awaddr[1]    (haddr_to_ahb2apb),
        // ... other slave signals to/from AHB2APB ...

        // ... other slave ports ...
    );
    ```

#### 3.1.4. AHB2APB 桥模块
*   **推荐做法**: 本代码库已在 `rtl/e203/general/sirv_gnrl_icbs.v` 提供 `sirv_gnrl_icb2apb`，并在 `rtl/e203/subsys/e203_subsys_perips.v` 大量实例化。因此通常**不再需要**额外 AHB2APB；若坚持 AHB 统一访问，可外接标准 AHB2APB IP 并映射到 `0x1000_0000` 区间。
*   **关注点**:
    *   **AHB 从接口**: 将此桥的 AHB 从接口连接到 AHB 总线矩阵的一个从端口。
    *   **APB 主接口**: 此桥的 APB 主接口将连接到系统中的 APB 从设备，如图中的"配置信息 (regfile)"。
    *   **地址译码**: 桥内部或外部需要 APB 地址译码逻辑，以选择连接到其 APB 接口的多个 APB 从设备中的一个。
    *   **参数配置**: 可能有参数用于配置 APB 总线的数量或数据宽度（通常为32位）。

#### 3.1.5. SoC 顶层文件 (`soc_top.v` 或类似)
*   **可能路径**: `rtl/e203/soc/`
*   **关注点**: 这是所有模块被例化和连接的地方。
    *   **例化**: 确保 E203 核、CIB2AHB、AHB 总线矩阵、AHB2APB 桥、内存控制器、DMA、网络接口等所有关键模块都被正确例化。
    *   **连接**: 实现模块间的连线，特别是总线信号的连接。
    *   **时钟和复位**: 生成并分发系统时钟 (`hclk`, `core_clk` 等) 和复位信号 (`hresetn`, `core_resetn` 等)。
    *   **地址映射定义**: 通常在 SoC 顶层或专门的地址映射配置文件中定义整个系统的地址空间。

### 3.2. 地址空间分配

#### 3.2.1. 系统地址映射规划
在集成之前，必须有一个清晰的系统地址映射规划。这张"地图"规定了系统中每个内存区域和外设寄存器在物理地址空间中的位置。

*   **示例地址映射表 (仅为示意，具体值需您根据系统需求定义)**:

    | 设备/区域             | 起始地址    | 结束地址    | 大小    | 连接到 (AHB Slave Port) | 备注                                   |
    | --------------------- | ----------- | ----------- | ------- | ----------------------- | -------------------------------------- |
    | Boot ROM              | `0x0000_0000` | `0x0000_FFFF` | 64KB    | AHB Matrix (Slave X)    | 存放启动代码                           |
    | DDR/SRAM              | `0x8000_0000` | `0xBFFF_FFFF` | 1GB     | AHB Matrix (Slave Y)    | 主内存                                 |
    | AHB2APB Bridge (Perips) | `0x1000_0000` | `0x1000_FFFF` | 64KB    | AHB Matrix (Slave Z)    | APB 外设从此基地址开始映射             |
    |   - UART0 (APB)       | `0x1000_0000` | `0x1000_00FF` | 256B    |   (via AHB2APB)         | 属于 AHB2APB 桥的 APB 地址空间       |
    |   - GPIO (APB)        | `0x1000_0100` | `0x1000_01FF` | 256B    |   (via AHB2APB)         | 属于 AHB2APB 桥的 APB 地址空间       |
    |   - Regfile (APB)     | `0x1000_1000` | `0x1000_1FFF` | 4KB     |   (via AHB2APB)         | 系统配置寄存器，如图中所示         |
    | DMA0 Controller Regs  | `0x2000_0000` | `0x2000_0FFF` | 4KB     | AHB Matrix (Slave A)    | DMA0 控制寄存器                      |
    | DMA1 Controller Regs  | `0x2001_0000` | `0x2001_0FFF` | 4KB     | AHB Matrix (Slave B)    | DMA1 控制寄存器                      |
    | DMA2 Controller Regs  | `0x2002_0000` | `0x2002_0FFF` | 4KB     | AHB Matrix (Slave C)    | DMA2 控制寄存器                      |
    | 网络接口 Regs         | `0x3000_0000` | `0x3000_FFFF` | 64KB    | AHB Matrix (Slave D)    | 网络接口配置和数据端口               |
    | ...其他从设备...      | ...         | ...         | ...     | ...                     | ...                                    |

*   **注意事项**:
    *   地址区域不能重叠。
    *   地址边界应对齐，便于译码。
    *   为未来的扩展预留一些地址空间。

#### 3.2.2. E203 视角下的地址映射
E203 处理器本身通常不直接感知完整的系统地址映射。它通过其总线接口发出物理地址。CIB2AHB 桥将这些物理地址传递到 AHB 总线矩阵。
*   **启动地址**: E203 复位后，会从一个固定的启动地址 (通常是 `0x0000_0000` 或可配置) 开始取第一条指令。确保该地址映射到存放了有效启动代码的 Boot ROM 或 Flash。
*   **内存保护 (PMP)**: 如果 E203 配置了物理内存保护 (PMP) 单元，需要在软件中正确配置 PMP 区域以匹配系统地址映射，从而允许或禁止对特定内存区域的访问。

#### 3.2.3. 修改地址译码逻辑
地址译码逻辑是确保 AHB 主设备（如 E203）的请求能够被正确路由到目标 AHB 从设备的关键。
*   **位置**: 地址译码器通常是 AHB 总线矩阵的一部分，或者是一个独立的模块，其输出 (`HSELx` 信号) 连接到 AHB 总线矩阵的从设备选择端口或直接连接到各个从设备。
*   **实现**: 对于每个 AHB 主设备接口到 AHB 总线矩阵的连接，当一个主设备发起事务时，总线矩阵内部的译码器会比较 `HADDR` 与预定义的各个从设备的地址范围。
    *   当 `HADDR` 落入某个从设备的地址范围时，对应的 `HSELx` 信号会被拉高，选中该从设备。
*   **修改方法**: 您需要根据 3.2.1 节中规划的地址映射表，在 RTL 代码中实现或修改这个译码逻辑。这通常涉及到比较器和逻辑门。
    *   在参数化的总线矩阵 IP 中，地址映射可能通过设置参数或配置寄存器来完成。
    *   在自定义的 RTL 代码中，可能需要直接修改 Verilog/VHDL 代码中的 `assign HSEL_DEVICE_X = (HADDR >= DEVICE_X_BASE_ADDR) && (HADDR <= DEVICE_X_END_ADDR);` 之类的语句。

    ```verilog
    // 概念性地址译码逻辑 (在总线矩阵内部或作为独立模块)
    // 输入: HADDR (来自当前获得总线授权的主设备)
    // 输出: HSEL_DDR_SRAM, HSEL_AHB2APB, HSEL_DMA0_REGS, ... (选择各个从设备)

    localparam DDR_SRAM_BASE     = 32'h8000_0000;
    localparam DDR_SRAM_SIZE     = 32'h4000_0000; // 1GB
    localparam DDR_SRAM_END      = DDR_SRAM_BASE + DDR_SRAM_SIZE - 1;

    localparam AHB2APB_BASE      = 32'h1000_0000;
    localparam AHB2APB_SIZE      = 32'h0001_0000; // 64KB
    localparam AHB2APB_END       = AHB2APB_BASE + AHB2APB_SIZE - 1;

    // ... 定义其他从设备的基地址和大小 ...

    assign HSEL_DDR_SRAM   = (HADDR >= DDR_SRAM_BASE) && (HADDR <= DDR_SRAM_END);
    assign HSEL_AHB2APB    = (HADDR >= AHB2APB_BASE)  && (HADDR <= AHB2APB_END);
    // ... 其他 HSEL 信号的分配 ...

    // 确保同一时间只有一个 HSEL 有效 (通常由总线矩阵保证，或译码逻辑设计保证互斥)
    ```

### 3.3. 在 AHB 矩阵中集成 E203 (作为主设备)
E203 通过 CIB2AHB 桥连接到 AHB 总线矩阵的一个主端口。

#### 3.3.1. AHB 主设备接口连接
如 3.1.2 和 3.1.3 节中的代码示例所示，关键是将 CIB2AHB 桥输出的 AHB 主接口信号（`HADDR`, `HWRITE`, `HWDATA`, `HTRANS`, `HSIZE`, `HBURST`, `HPROT`, `HMASTLOCK` 等）正确连接到 AHB 总线矩阵对应的主端口输入。同时，将 AHB 总线矩阵该主端口的输出（`HRDATA`, `HREADYIN` (来自被选中从设备的HREADY), `HRESP`）连接回 CIB2AHB 桥的对应输入。

*   **位宽匹配**: 确保 CIB2AHB 输出的 AHB 接口位宽 (32位) 与 AHB 总线矩阵主端口的期望位宽一致。如果矩阵主端口是64位的，而 CIB2AHB 输出是32位的，则需要一个数据宽度转换器 (upsizer) 来进行适配，但这会增加复杂性。根据图示，E203 到 AHB Matrix 的连接是32位的，而 Matrix 到 DDR/SRAM 等是64位的。这意味着 AHB Matrix 本身或其连接的从设备侧需要处理位宽转换的问题，或者说 E203 只能以32位模式访问64位从设备（例如，一个64位读需要两次32位读，或通过特殊的桥接逻辑实现）。这将在"集成挑战"部分详细讨论。
    *   **实际情况**：CIB2AHB 输出的 AHB 接口是32位的。当这个32位主设备要访问一个64位的从设备（如DDR/SRAM）时，AHB总线矩阵或者一个专门的32位到64位桥（如果存在的话）需要处理这个问题。标准的 AHB 协议允许不同位宽的主从设备通过总线互联，但通常要求主设备能正确发出 `HSIZE` 来指示其访问的宽度，并且能够处理多次传输来完成一个更大宽度的操作（如果需要的话）。对于 E203，它通过32位接口发出32位访问。如果它要访问64位宽的内存，那么对64位内存的每次访问，E203 仍会是发起32位的读/写。64位内存控制器需要能响应32位的访问请求。例如，一个64位的内存位置，E203 可以通过两个独立的32位访问来读取其低32位和高32位。

#### 3.3.2. 总线矩阵仲裁配置
AHB 总线矩阵允许多个主设备共享总线。因此，仲裁是必不可少的。
*   **仲裁器 (Arbiter)**: 位于 AHB 总线矩阵内部，负责决定在多个主设备同时请求总线访问时，哪个主设备获得授权。
*   **仲裁算法**: 常见的算法有：
    *   **固定优先级 (Fixed Priority)**: 为每个主设备分配一个固定的优先级。高优先级主设备总是优先获得总线。需要合理分配优先级，避免低优先级主设备饿死。
    *   **轮询 (Round-Robin)**: 主设备轮流获得总线访问权，相对公平。
    *   **LRU (Least Recently Used)**: 最近最少使用的主设备获得较高优先级。
    *   **加权轮询 (Weighted Round-Robin)**: 根据权重分配访问机会。
*   **配置方法**: 如果您使用的是可配置的 AHB 矩阵 IP，通常可以通过设置 IP 的参数或通过配置端口在运行时（较少见）来选择仲裁算法和设置优先级。
    *   例如，会有类似 `PRIORITY_MASTER0 = 3`, `PRIORITY_MASTER1 = 1` 这样的参数用于设定主设备的优先级。
*   **E203 的优先级**: 通常，CPU (E203) 需要相对较高的优先级以保证系统的响应性，但不能过高以至于阻塞其他关键主设备（如实时性要求高的 DMA）。需要根据系统整体性能需求进行权衡。

### 3.4. AHB2APB 桥的连接与配置
AHB2APB 桥用于连接低速的 APB 外设。根据系统图，**配置信息 (regfile)** 是通过此桥被 E203 访问的。

#### 3.4.1. APB 总线外设连接
*   **AHB 从接口**: AHB2APB 桥的 AHB 从接口连接到 AHB 总线矩阵的一个从端口。其地址范围已在系统地址映射中定义 (例如 `0x1000_0000` - `0x1000_FFFF`)。
*   **APB 主接口**: 桥的 APB 主接口 (`PADDR`, `PWDATA`, `PRDATA`, `PWRITE`, `PSELx`, `PENABLE`, `PREADY`, `PSLVERR`) 连接到一个或多个 APB 从设备。
*   **APB 从设备实例化与连接**: 在 SoC 顶层或 APB 子系统中实例化 APB 外设（如 UART, GPIO, Timer, 以及图中的 `regfile`），并将它们的 APB 从接口连接到 AHB2APB 桥的 APB 主接口。
    ```verilog
    // 概念性 - APB 外设连接到 AHB2APB 桥
    wire        apb_psel_regfile;
    wire [31:0] apb_paddr_to_regfile; // PADDR from bridge, sliced for regfile
    // ... 其他 APB 信号 ...

    ahb2apb_bridge u_ahb2apb_bridge (
        // AHB Slave Interface (to AHB Matrix)
        .HCLK       (hclk),
        .HRESETn    (hresetn),
        .HSEL       (hsel_for_ahb2apb_bridge), // From AHB Matrix/Decoder
        .HADDR      (haddr_to_ahb2apb_bridge), // From AHB Matrix
        // ... other AHB slave signals ...

        // APB Master Interface (to APB peripherals)
        .PCLK       (pclk), // APB clock, can be same as HCLK or slower
        .PRESETn    (presetn),
        .o_PADDR    (apb_paddr_out_of_bridge),
        .o_PSEL     (apb_psel_out_of_bridge), // This will be an array if multiple APB slaves
        // ... other APB master output signals ...
        .i_PRDATA   (apb_prdata_to_bridge),
        .i_PREADY   (apb_pready_to_bridge),
        .i_PSLVERR  (apb_pslverr_to_bridge)
    );

    // APB 外设: Regfile
    // APB 地址译码 (通常在桥内部，或桥外部基于 apb_paddr_out_of_bridge 和 apb_psel_out_of_bridge[index] )
    // 假设 Regfile 的 APB 选择信号是 apb_psel_out_of_bridge[0]
    // 并且其在 APB 地址空间中的基地址是 0x1000 (相对于 AHB2APB 桥的基地址 0x1000_0000)
    assign apb_psel_regfile = apb_psel_out_of_bridge[REGFILE_APB_INDEX] && 
                              (apb_paddr_out_of_bridge[APB_ADDR_WIDTH-1:0] >= REGFILE_APB_BASE_OFFSET) && 
                              (apb_paddr_out_of_bridge[APB_ADDR_WIDTH-1:0] <= REGFILE_APB_END_OFFSET);

    regfile_module u_regfile (
        .PCLK       (pclk),
        .PRESETn    (presetn),
        .PADDR      (apb_paddr_out_of_bridge[REGFILE_ADDR_BITS-1:0]), // Pass relevant address bits
        .PSEL       (apb_psel_regfile),
        .PENABLE    (apb_penable_from_bridge), // PENABLE from bridge
        .PWRITE     (apb_pwrite_from_bridge),
        .PWDATA     (apb_pwdata_from_bridge),
        .o_PRDATA   (prdata_from_regfile),
        .o_PREADY   (pready_from_regfile),
        .o_PSLVERR  (pslverr_from_regfile)
    );

    // Logic to combine PRDATA/PREADY/PSLVERR from multiple APB slaves to bridge
    // This is often handled by an APB interconnect fabric if multiple slaves exist
    assign apb_prdata_to_bridge = apb_psel_regfile ? prdata_from_regfile : DEFAULT_PRDATA;
    assign apb_pready_to_bridge = apb_psel_regfile ? pready_from_regfile : DEFAULT_PREADY_WHEN_NO_SLAVE_SELECTED;
    assign apb_pslverr_to_bridge= apb_psel_regfile ? pslverr_from_regfile : 1'b0;
    ```

#### 3.4.2. 配置寄存器访问 (regfile)
图中的"配置信息 (regfile)"模块是一个通过 APB 总线访问的从设备。E203 需要通过 AHB 总线 -> AHB 总线矩阵 -> AHB2APB 桥 -> APB 总线 -> `regfile` 这样的路径来读写这些寄存器。
*   **RTL 实现**: `regfile` 自身是一个标准的 APB 从设备模块，内部包含若干可读写寄存器。
*   **软件访问**: 驱动程序或固件代码中，通过访问分配给 `regfile` 的内存映射地址 (例如 `0x1000_1000` 到 `0x1000_1FFF`) 来配置系统参数。

### 3.5. 最小化修改 E203 现有代码的策略
目标是尽可能少地修改 E203 处理器核本身的代码，而是通过外围的桥接和 SoC 集成逻辑来适配。
1.  **使用标准接口**: E203 的 ICB 接口是其与外部世界的标准连接方式。集成工作应主要集中在实现或配置好 ICB 到目标总线（AHB）的桥。
2.  **参数化配置**: 优先使用 E203 核、总线桥、总线矩阵等模块提供的参数来进行配置，而不是直接修改 RTL 源码。例如，E203 的某些特性（如 TCM 大小、调试接口类型）可能是通过 Verilog `parameter` 或 `localparam` 在例化时配置的。
3.  **模块化设计**: 将特定于应用的逻辑（如特殊的内存控制器接口、自定义加速器接口）封装在独立的模块中，而不是混入处理器核或标准总线组件中。
4.  **SoC 顶层进行集成**: 大部分的连接、地址译码、仲裁配置等工作都在 SoC 顶层或专门的 SoC 子系统模块中完成，处理器核作为一个黑盒被例化。
5.  **不修改处理器流水线或指令集**: 除非进行微架构级别的深度定制，否则应避免修改 E203 的核心流水线、指令译码器等关键内部逻辑。

通过遵循这些策略，可以最大限度地重用经过验证的 E203 处理器核代码，减少引入错误的风险，并简化未来的升级和维护。

## 4. 集成挑战与解决方案

将 E203 处理器集成到如图所示的复杂 AHB 总线矩阵系统中，会遇到一系列技术挑战。本章节将讨论这些主要挑战并提供相应的解决策略。

### 4.1. 多主设备环境下的总线仲裁
**挑战**: 系统中有多个 AHB 主设备（E203 CPU, DMA0, DMA1, DMA2, 网络接口）竞争访问共享的 AHB 总线资源（如 DDR/SRAM 内存、AHB2APB 桥）。必须有一个高效且公平的仲裁机制来管理总线访问权，防止冲突并确保系统性能。

**解决方案**:
1.  **AHB 总线矩阵内置仲裁器**: AHB 总线矩阵的核心功能之一就是仲裁。您需要配置或选择合适的仲裁算法。
    *   **固定优先级 (Fixed Priority)**: 为每个主设备分配一个静态优先级。例如，CPU (E203) 通常具有较高优先级以保证指令执行的流畅性；DMA 在进行大数据块传输时也可能需要高优先级以避免数据丢失或超时。
        *   *优点*: 实现简单，关键主设备响应快。
        *   *缺点*: 低优先级主设备可能长时间等待（饿死）。
    *   **轮询 (Round-Robin)**: 各个主设备轮流获得访问权。
        *   *优点*: 相对公平，避免饿死。
        *   *缺点*: 可能无法保证关键主设备的实时响应。
    *   **加权轮询 (Weighted Round-Robin, WRR)**: 根据预设权重为不同主设备分配不同的访问机会。
    *   **LRU (Least Recently Used)**: 最近最少使用的主设备获得较高优先级。
2.  **优先级配置**: 根据系统需求仔细配置仲裁优先级。例如：
    *   E203 CPU: 通常较高，保证系统控制流。
    *   DMA (特别是服务于 DSP 或网络接口的 DMA): 可能需要高优先级，以满足实时数据传输需求。
    *   网络接口: 根据其带宽和延迟敏感度设置。
3.  **避免死锁和活锁**: 确保仲裁逻辑不会导致任何主设备永远无法获得总线访问（死锁），或在不同主设备间无意义地快速切换（活锁）。
4.  **可配置性**: 理想情况下，仲裁策略和优先级应该是可配置的，以便在系统调试和优化阶段进行调整。

### 4.2. 地址映射与内存区域划分
**挑战**: 正确规划和实现整个系统的地址映射至关重要。地址冲突、错误的区域大小或访问权限设置会导致系统故障。

**解决方案**:
1.  **统一的地址映射表**: 如 3.2.1 节所述，在设计初期就制定详细且无歧义的地址映射表，明确每个从设备的基地址、大小和访问属性。
2.  **AHB 译码器实现**: 在 AHB 总线矩阵或其外围实现精确的地址译码逻辑，根据主设备发出的 `HADDR` 信号正确生成各个从设备的 `HSELx` 信号。
    *   确保译码逻辑覆盖所有已定义的地址空间，并且没有重叠区域。
    *   为未映射的地址访问提供明确的错误响应机制（例如，AHB 总线矩阵可以为无效地址返回 `HRESP=ERROR`）。
3.  **E203 PMP/MMU 配置**: 如果 E203 使用了物理内存保护 (PMP) 或内存管理单元 (MMU)，确保其配置与系统级地址映射一致，以实现正确的内存访问控制和保护。
4.  **APB 地址映射**: 对于通过 AHB2APB 桥连接的 APB 外设，还需要在 APB 域内进行二级地址译码。
5.  **文档化**: 详细记录地址映射，供硬件和软件工程师参考。

### 4.3. 数据宽度不匹配 (32位 E203 vs 64位 AHB/SRAM)
**挑战**: 系统图显示 E203 通过 CIB2AHB 桥以 32 位接口连接到 AHB 矩阵，而 DDR/SRAM、DMA 和网络接口等是 64 位接口。这种数据宽度不匹配需要妥善处理。

#### 4.3.1. 数据位宽转换逻辑

### 4.4. 时钟域同步 (Clock Domain Crossing - CDC)
**挑战**: 一个复杂的 SoC 通常包含多个时钟域。例如，E203 CPU 核可能运行在一个时钟频率，AHB 总线在另一个频率，而某些外设（如网络接口的 MAC/PHY，DDR 控制器的 PHY）可能有其自身的时钟。跨时钟域的数据和控制信号传输必须小心处理，以避免亚稳态和数据丢失。

**解决方案**:
1.  **识别时钟域**: 清晰地标识出系统中所有的时钟域及其关系（同步、异步、倍频/分频）。
2.  **同步器 (Synchronizers)**: 对于单比特控制信号跨异步时钟域传输，使用标准的两级或三级触发器同步器来降低亚稳态的概率。
    *   例如，中断信号、复位信号（如果跨域）等。
3.  **异步 FIFO (Asynchronous FIFO)**: 对于多比特数据或需要较高吞吐率的跨异步时钟域传输，使用异步 FIFO 是最可靠和常用的方法。
    *   异步 FIFO 使用独立的读写时钟，并通过格雷码 (Gray code) 实现的读写指针比较来判断 FIFO 的空/满状态，从而安全地处理 CDC。
    *   CIB2AHB 桥（连接 E203 核时钟域和 AHB 总线时钟域）、AHB2APB 桥（连接 AHB 时钟域和 APB 时钟域，如果二者异步）、DMA 控制器（其内部不同接口可能对应不同时钟域）等模块，如果其两侧连接到不同时钟域的接口，其内部通常会使用异步 FIFO 或其他形式的 CDC 机制 (如双口RAM配合握手信号) 来保证数据和控制信号的可靠传输。
    *   系统图中，E203 (core clk) -> CIB2AHB -> AHB Matrix (hclk) -> DDR/SRAM (mem_clk)。如果这些时钟不同，则需要在桥或接口处进行同步。
4.  **握手协议**: 对于控制流或低带宽数据，可以使用跨时钟域的握手协议。发送方发出请求，等待接收方在自己的时钟域确认后才撤销请求。这种方法相对较慢但可靠。
5.  **静态时序分析 (STA)**: 使用 STA 工具仔细分析所有 CDC 路径，确保同步逻辑的正确性和时序约束的满足。
6.  **避免组合逻辑跨域**: 严禁组合逻辑的输出直接连接到另一个时钟域的输入，这极易导致亚稳态。

### 4.5. 复位机制协调
**挑战**: 系统中所有模块必须在正确的时刻以正确的顺序复位，以确保系统启动到已知状态。不正确的复位会导致模块功能异常或整个系统无法启动。

**解决方案**:
1.  **全局复位与局部复位**: 通常有一个全局的系统复位信号 (例如上电复位 `POR_n`，或按钮复位 `RESET_n`)。
    *   此全局复位信号需要被正确地同步到各个模块的时钟域（如果它们处于不同时钟域），然后驱动这些模块的复位输入 (通常是低有效，如 `hresetn`, `presetn`, `core_resetn`)。
2.  **复位同步**: 对于异步复位信号，如果它被释放（变为无效）时，其释放边沿必须相对于接收模块的时钟是同步的，以避免触发器进入亚稳态。这通常通过"异步置位，同步释放"的复位同步器实现。
3.  **复位序列**: 某些复杂的模块（如 DDR 控制器、PLL）可能有特定的复位序列要求。SoC 的复位逻辑需要保证这些序列得到满足。
4.  **AHB/APB 复位**: AHB 总线有 `HRESETn`，APB 总线有 `PRESETn`。这些信号必须在对应的总线时钟 (`HCLK`, `PCLK`) 的有效边沿之后若干个周期内保持有效，以确保所有总线上的主从设备都已正确复位。
5.  **E203 核复位**: E203 核有其自身的复位输入。确保其在核心时钟稳定后被正确复位。
6.  **软件可控复位**: 某些外设可能需要或支持通过软件写入寄存器来进行局部复位。

妥善处理这些集成挑战是保证 SoC 系统稳定可靠运行的关键。

## 5. 性能优化

在成功集成 E203 处理器和 AHB 系统后，性能优化是提升系统整体效率的关键步骤。本章节将讨论几个重要的性能优化方向。

### 5.1. E203 访问内存的延迟分析与优化
**挑战**: E203 CPU 访问外部内存（如 DDR/SRAM）的延迟直接影响处理器性能。延迟包括 ICB 总线传输、CIB2AHB 桥转换、AHB 总线矩阵仲裁和路由、以及内存控制器本身的延迟。

**解决方案**:
1.  **流水线与等待状态分析**:
    *   **测量延迟**: 通过仿真或硬件性能计数器（如果 E203 支持）测量平均内存访问延迟。
    *   **定位瓶颈**: 分析延迟的各个组成部分，找出主要的贡献者。是总线仲裁等待时间过长？是桥转换引入了过多周期？还是内存控制器响应慢？
2.  **优化 CIB2AHB 桥**: 确保桥的实现尽可能高效，状态转换最小化，避免不必要的等待周期。
3.  **AHB 总线矩阵配置**: 优化仲裁算法和优先级，减少 E203 在高负载情况下的等待时间。
4.  **内存控制器调优**: 配置内存控制器（如 DDR 控制器）的参数，如时序参数、刷新率等，以在满足稳定性的前提下获得最佳性能。
5.  **使用 TCM (Tightly Coupled Memory)**:
    *   **ITCM (Instruction TCM)**: 对于性能关键且频繁执行的代码段（如中断服务程序、核心算法），将其放入 ITCM 可以显著降低取指延迟，因为 ITCM 通常是单周期或极低延迟访问的 SRAM，直接连接到 CPU，绕过了大部分总线开销。
    *   **DTCM (Data TCM)**: 对于频繁访问的关键数据结构或堆栈，放入 DTCM 可以大幅提升数据访问速度。
    *   `e203_defines.v` 中有 `E203_HAS_ITCM` 和 `E203_HAS_DTCM` 宏，表明您的 E203 配置可能支持 TCM。您需要在软件中通过链接脚本将代码和数据放置到 TCM 的地址空间。
6.  **预取机制 (Prefetching)**:
    *   **E203 IFU 预取**: E203 的指令获取单元 (IFU) 可能内置了指令预取逻辑 (例如，在 `e203_ifu_ifetch.v` 中可以看到相关的预取控制)，可以在当前指令执行的同时获取后续的指令，以减少取指停顿。理解其预取深度和条件，并尽量编写有助于发挥其效能的代码（例如，优化分支预测，减少不必要的分支跳转，保持代码的线性执行流）可以提升性能。
    *   **DMA 预取**: 对于可预测的数据访问模式（如 DSP 处理的流数据），可以使用 DMA 提前将数据从主内存预取到 SRAM (如系统图中的 sram0, sram1) 或 DTCM，供 CPU 或 DSP 核高速访问。
7.  **减少非对齐访问**: 虽然处理器和总线可能支持非对齐访问，但它们通常比对齐访问慢得多，因为可能需要多次总线事务来完成。在软件层面应尽可能保证数据结构的自然对齐，特别是在性能敏感的代码中。

### 5.2. 多主设备争用时的性能保障
**挑战**: 当多个 AHB 主设备（E203, DMAs, 网络接口）同时高负载运行时，对共享资源（特别是 DDR/SRAM）的争用会加剧，可能导致某些关键任务的性能下降或不确定性。

**解决方案**:
1.  **合理的仲裁策略**: 如 4.1 节所述，选择或配置能够平衡公平性和实时性的仲裁算法。固定优先级可能适用于某些场景，但需要小心饿死问题。加权轮询或基于 QoS 的仲裁可能更优。
2.  **QoS (Quality of Service) 机制**: 一些高级的 AHB 总线矩阵或互联网络支持 QoS 机制。
    *   可以为不同主设备或不同类型的事务（如读 vs. 写，实时 vs. 非实时）分配不同的 QoS 等级。
    *   仲裁器会根据 QoS 等级来优先处理高 QoS 请求，即使其静态优先级较低。
    *   这需要硬件（总线矩阵支持 QoS 功能）和软件（通过配置寄存器设置 QoS 等级）协同工作。
3.  **总线带宽分配**: 分析各个主设备的带宽需求，确保总线和内存系统的总带宽能够满足高峰期需求。
    *   如果带宽不足，考虑增加总线位宽（如从32位到64位，图中已部分实现）、提高总线频率（需考虑时序收敛）、或使用多端口内存控制器。
4.  **流量整形与调度**: 对于 DMA 传输，可以通过软件控制其启动时间、传输速率和突发长度，以避免与 CPU 的关键操作发生长时间冲突。
5.  **分离总线或使用多层总线**: 对于极高带宽或低延迟要求的关键路径，可以考虑使用专用的总线或内存端口，而不是完全依赖共享的 AHB 总线矩阵。例如，DSP 核的数据通路（sram0, sram1, sram2）实际上就是一种专用高速通路，通过 DMA 与主 AHB 系统解耦。

### 5.3. 缓存策略调整建议 (E203 L1 Cache)
**挑战**: E203 处理器核通常包含 L1 指令缓存 (I-Cache) 和 L1 数据缓存 (D-Cache)。缓存的命中率和替换策略直接影响 CPU 性能。不当的缓存使用或配置（如错误的内存区域可缓存属性）会导致性能下降甚至功能错误。

**解决方案**:
1.  **使能和配置缓存**: 确保在 E203 的配置中使能了 I-Cache 和 D-Cache (如果硬件支持)。检查相关的 CSR (Control and Status Registers) 来控制缓存的使能/禁用状态。
2.  **内存区域属性 (Cacheability & Bufferability)**:
    *   **PMP/MMU**: E203 的物理内存保护 (PMP) 单元或内存管理单元 (MMU, 如果存在) 通常用于定义不同内存区域的属性，包括是否可缓存 (Cacheable) 和是否可写缓冲 (Bufferable)。
    *   **正确设置**: 必须为系统中的每个主要内存区域（DDR/SRAM, TCM, 外设寄存器空间）正确设置这些属性。
        *   **DDR/SRAM**: 通常设置为可缓存和可写缓冲，以获得最佳性能。
        *   **TCM**: 通常不应被缓存，因为它们是快速的本地内存。
        *   **外设寄存器空间 (MMIO - Memory-Mapped I/O)**: **绝对不能设置为可缓存**。对外设寄存器的读写必须是精确的、非缓冲的、非缓存的，以确保操作的实时性和副作用的正确发生。错误的缓存配置会导致读取到过时的数据或写操作没有及时到达外设。
    *   这些属性会通过 ICB 总线的 `icb_cmd_prot` (如果存在) 或其他机制传递给 CIB2AHB 桥，并最终转换为 AHB 总线的 `HPROT` 信号的相应位 (`HPROT[3]` for Cacheable, `HPROT[2]` for Bufferable)。
3.  **缓存一致性 (Coherency)**:
    *   在有 DMA 或其他总线主设备可以直接修改内存（特别是被 CPU 缓存的内存区域）的系统中，必须处理缓存一致性问题。
    *   E203 这样的小型嵌入式核通常不包含硬件缓存一致性协议 (如 MESI)。
    *   **软件管理**: 一致性通常需要通过软件显式管理：
        *   **缓存刷新 (Flush/Clean)**: 在 DMA 读取 CPU 修改过的数据之前，CPU 需要将相应缓存行（脏数据）写回到主内存。
        *   **缓存无效 (Invalidate)**: 在 CPU 读取 DMA 修改过的内存区域之前，CPU 需要将相应的缓存行作废，以强制从主内存重新加载新数据。
        *   RISC-V 提供了 `FENCE` 和 `FENCE.I` 指令，以及针对特定缓存操作的自定义指令或 CSR (如果实现的话) 来辅助软件进行缓存管理。
4.  **缓存替换策略**: E203 的 L1 缓存通常使用简单的替换策略，如 LRU (Least Recently Used) 或伪 LRU。这通常是硬件固定的，软件无法直接修改，但了解其行为有助于编写缓存友好的代码。
5.  **代码和数据布局**: 组织代码和数据以提高空间局部性和时间局部性，从而提升缓存命中率。
    *   例如，将频繁一起访问的数据放在连续的内存中。
    *   循环优化，如循环分块 (Loop Tiling)，可以改善数据缓存的利用率。

通过综合考虑这些方面，可以有效地提升 E203 系统在 AHB 总线环境下的整体性能。

## 6. 调试与测试

在复杂的 SoC 集成项目中，调试与测试是确保系统功能正确性、稳定性和性能达标不可或缺的环节。本章节将介绍针对 E203 与 AHB 总线系统集成的调试策略和测试方法。

### 6.1. 总线信号监控点设置
**挑战**: 当系统行为不符合预期时，需要观测关键的总线信号来定位问题。直接探测 FPGA/ASIC 内部所有信号是不现实的，因此需要预先规划重要的监控点。

**解决方案**:
1.  **ILA (Integrated Logic Analyzer) / Signal Tap**: FPGA 供应商（如 Xilinx Vivado ILA, Intel Quartus Signal Tap）提供了嵌入式逻辑分析仪工具。可以在 RTL 设计中例化这些 IP 核，选择需要观测的关键信号，并在硬件运行时捕捉这些信号的波形。
2.  **关键信号列表**: 针对 E203 与 AHB 总线的集成，以下是一些强烈建议监控的信号组：
    *   **E203 ICB 接口 (CIB2AHB 桥的 ICB 侧)**:
        *   `[ifu/lsu]_icb_cmd_valid`, `[ifu/lsu]_icb_cmd_ready`, `[ifu/lsu]_icb_cmd_addr`
        *   `lsu_icb_cmd_read`, `lsu_icb_cmd_wdata`, `lsu_icb_cmd_wmask` (LSU)
        *   `[ifu/lsu]_icb_rsp_valid`, `[ifu/lsu]_icb_rsp_ready`, `[ifu/lsu]_icb_rsp_rdata`, `[ifu/lsu]_icb_rsp_err`
        *   *目的*: 确认 CPU 是否正确发出请求，桥是否正确响应，数据是否正确传输。
    *   **CIB2AHB 桥的 AHB 主接口 (连接到 AHB 矩阵)**:
        *   `HCLK`, `HRESETn`
        *   `HADDR`, `HTRANS`, `HWRITE`, `HSIZE`, `HBURST`, `HPROT`, `HMASTLOCK`
        *   `HWDATA` (写操作时), `HRDATA` (读操作时)
        *   `HREADY` (输入到桥), `HRESP` (输入到桥)
        *   *目的*: 确认桥是否将 ICB 事务正确转换为 AHB 事务，AHB 时序是否符合规范，从设备响应是否正确。
    *   **AHB 总线矩阵的关键内部信号 (如果可观测)**:
        *   各个主设备的请求信号 (`HBUSREQx`)
        *   各个主设备的授权信号 (`HGRANTx`)
        *   选中从设备的 `HSELx` 信号
        *   仲裁器的状态信号
        *   *目的*: 诊断仲裁问题、路由问题、死锁等。
    *   **目标 AHB 从设备接口 (如 DDR/SRAM 控制器, AHB2APB 桥)**:
        *   `HSEL` (输入到从设备)
        *   `HADDR`, `HTRANS`, `HWRITE`, `HSIZE`, `HBURST`, `HPROT` (输入到从设备)
        *   `HREADY` (从设备输出), `HRESP` (从设备输出)
        *   *目的*: 确认请求是否正确到达从设备，从设备是否正确响应。
    *   **AHB2APB 桥的 APB 接口**:
        *   `PCLK`, `PRESETn`
        *   `PADDR`, `PSEL`, `PENABLE`, `PWRITE`, `PWDATA`, `PRDATA`, `PREADY`, `PSLVERR`
        *   *目的*: 确认 APB 事务是否正确，目标 APB 外设是否响应。
    *   **中断信号**: CPU 的中断请求线、PLIC (Platform-Level Interrupt Controller) 的输入输出。
    *   **DMA 控制器接口**: DMA 的 AHB 主/从接口信号，以及与 SRAM 的接口信号。
3.  **触发条件设置**: 善用 ILA 的触发功能。例如，当发生 AHB 错误响应 (`HRESP=ERROR`) 时触发，或者当 CPU 访问特定敏感地址时触发，或者当某个状态机进入异常状态时触发。
4.  **仿真波形对比**: 将硬件 ILA 捕捉到的波形与 RTL 仿真中的预期波形进行对比，有助于快速发现差异和问题。
5.  **调试端口/通路**: E203 核通常包含一个调试接口（如 JTAG），可以通过调试器（如 OpenOCD + GDB）来控制 CPU 运行、设置断点、观察寄存器和内存。这对于软件和硬件协同调试至关重要。

### 6.2. 验证策略与测试用例设计
**挑战**: 确保整个集成系统的功能正确性和鲁棒性需要全面且有层次的验证策略。

**解决方案**:
1.  **单元测试 (Module/IP Level Verification)**:
    *   对每个关键模块（E203 核本身、CIB2AHB 桥、AHB 总线矩阵、AHB2APB 桥、DMA 控制器、内存控制器、各个外设）进行独立的单元测试。
    *   使用 SystemVerilog 和 UVM (Universal Verification Methodology) 或类似的验证方法学可以提高测试的完备性和可重用性。
    *   测试用例应覆盖所有功能点、边界条件、异常情况和配置选项。
    *   例如，对于 CIB2AHB 桥，测试用例应覆盖所有 ICB 到 AHB 的事务类型转换、错误传递、等待状态处理等。
2.  **子系统集成测试**:
    *   将若干相关的模块组成子系统进行测试。例如：
        *   E203 + CIB2AHB + 一个简单的 AHB 从设备 (如 AHB RAM)。
        *   AHB 总线矩阵 + 多个虚拟 AHB 主从设备模型 (Bus Functional Models - BFMs)。
    *   重点测试模块间的接口匹配、基本交互和时序。
3.  **系统级集成测试 (SoC Level Verification)**:
    *   在完整的 SoC 环境下（RTL 仿真或 FPGA 原型）运行测试程序。
    *   **裸机程序**: 编写 C 或汇编语言的测试程序，直接在 E203 上运行，测试：
        *   CPU 基本功能（指令集测试、CSR 访问）。
        *   内存访问：读写 DDR/SRAM 的不同地址范围、不同数据模式。
        *   外设功能：通过 AHB2APB 桥访问 UART, GPIO, Timer, Regfile 等，验证其寄存器读写和基本功能。
        *   DMA 传输：配置 DMA 进行内存到内存、内存到外设（如果支持）的传输，验证数据完整性和传输正确性。
        *   中断处理：触发各种中断源，验证中断响应、PLIC 行为和中断服务程序的正确执行。
    *   **操作系统/RTOS 引导**: 如果系统计划运行 OS/RTOS，尝试引导一个最小化的系统，验证 OS 内核的基本功能（如任务调度、内存管理、驱动程序交互）。
    *   **压力测试**: 模拟高负载情况，例如多个 DMA 同时工作，CPU 密集计算，网络接口高吞吐量，测试系统的稳定性和性能瓶颈。
    *   **边界条件和错误注入**: 测试系统在异常输入或故障条件下的行为。例如，注入 AHB 总线错误，测试错误处理机制；测试无效地址访问等。
4.  **FPGA 原型验证**: 将设计下载到 FPGA 平台上进行实际硬件验证。FPGA 运行速度远高于 RTL 仿真，可以暴露一些在仿真中难以发现的真实硬件问题或时序问题。
    *   可以连接真实的外部设备（如 DDR 内存芯片、网络 PHY、传感器等）。
5.  **形式验证 (Formal Verification)**: 对于一些关键的控制逻辑或协议转换模块（如仲裁器、总线桥的状态机），可以考虑使用形式验证方法来穷尽检查其行为是否符合规范，有无死锁等。
6.  **代码覆盖率与功能覆盖率**: 使用覆盖率工具（如代码行覆盖率、条件覆盖率、FSM 状态覆盖率、功能覆盖点）来衡量测试的完备性，并指导补充测试用例。

### 6.3. 常见问题诊断与解决方法
**挑战**: 在调试过程中，可能会遇到各种各样的问题。了解常见问题的表象和可能的原因有助于快速定位和解决。

**解决方案 - 问题与可能原因/解决方法**:
1.  **CPU 无法启动/卡死**: (E203 不执行第一条指令或在某个地址停滞)
    *   **可能原因**: 复位问题（复位信号未正确作用或释放）；时钟问题（核心时钟未提供或不稳定）；启动代码问题（Boot ROM/Flash 内容错误或地址映射错误）；总线访问错误（取第一条指令时总线挂起或返回错误）；电源问题。
    *   **解决方法**: 检查复位和时钟信号波形 (ILA)；通过 JTAG 调试器连接 CPU，查看 PC 值和 CPU 状态；确认 Boot ROM/Flash 的地址和内容；检查取指相关的总线事务。
2.  **内存访问错误**: (读到错误数据，写操作无效，或 CPU 产生精确/非精确总线错误异常)
    *   **可能原因**: 地址译码错误（访问到错误的从设备或无效地址）；数据宽度不匹配处理错误；字节选通/HSIZE 转换错误；内存控制器配置错误或故障；CIB2AHB 桥逻辑错误；缓存一致性问题 (软件未正确 flush/invalidate)；PMP/MMU 配置错误导致访问权限不足。
    *   **解决方法**: 使用 ILA 监控 CPU 发出的地址/数据/控制信号以及目标从设备的响应；单步调试内存访问指令，查看寄存器和内存内容；仔细检查地址映射和译码逻辑；验证缓存操作和 PMP/MMU 设置。
3.  **外设不工作或行为异常**: (UART 无输出，GPIO 无法控制，Timer 不计数)
    *   **可能原因**: AHB2APB 桥未正确工作或配置；APB 地址译码错误；外设时钟未提供或频率错误；外设复位问题；外设寄存器读写错误（例如，由于缓存导致写操作未实际到达）；中断未正确配置或连接。
    *   **解决方法**: ILA 监控 AHB2APB 桥的 AHB 和 APB 接口信号；确认外设时钟和复位；单步调试外设驱动代码，检查寄存器读写值；确保 MMIO 区域未被缓存。
4.  **DMA 传输失败或数据损坏**:
    *   **可能原因**: DMA 控制寄存器配置错误（源/目标地址、长度、方向、模式）；总线仲裁导致 DMA 超时或带宽不足；源/目标内存区域访问权限问题；数据宽度配置错误；时钟域同步问题（如果 DMA 跨时钟域）。
    *   **解决方法**: 仔细检查 DMA 配置参数；ILA 监控 DMA 的 AHB 主/从接口以及其与 SRAM 的接口；验证 DMA 访问的内存区域属性；确保 DMA 控制器和相关总线有足够的时钟周期完成操作。
5.  **性能不达标**: (系统运行缓慢，CPU 利用率异常高)
    *   **可能原因**: 总线争用严重；内存访问延迟过高；缓存命中率低；TCM 未有效利用；软件算法效率低下；时钟频率配置不当。
    *   **解决方法**: 参考第 5 节性能优化内容；使用性能分析工具（profiler）定位软件瓶颈；ILA 分析总线事务，查找等待周期和瓶颈点；优化缓存使用和 TCM 分配。
6.  **中断响应异常**: (中断不触发，触发错误的中断，或中断处理后系统行为异常)
    *   **可能原因**: 中断源未正确使能；PLIC 配置错误（优先级、阈值、使能）；中断信号连接问题；中断向量表或中断服务程序错误；中断嵌套处理不当；CPU 中断屏蔽（如 `MIE` 位未设置）。
    *   **解决方法**: JTAG 调试器查看 CPU 中断相关 CSRs (`MIE`, `MIP`, `MEPC`, `MCAUSE`)；ILA 监控中断控制器和 CPU 的中断信号；单步调试中断服务程序。

细致的规划、分阶段的验证以及善用调试工具是应对这些挑战的关键。

## 7. 实现路线图

### 7.1. 推荐的渐进式实现步骤

#### 7.1.1. 步骤一：基础 E203 系统搭建 (单主模式)

#### 7.1.2. 步骤二：引入 AHB 总线矩阵和内存

#### 7.1.3. 步骤三：集成 AHB2APB 桥和基础外设

#### 7.1.4. 步骤四：集成其他 AHB 主设备 (如 DMA, 网络接口)

#### 7.1.5. 步骤五：集成 4x4 DSP 核心

### 7.2. 关键验证点与里程碑

### 7.3. 最小可行产品 (MVP) 实现建议

## 8. 附录

### 8.1. 相关术语解释

### 8.2. 参考资料
