Hughger/graduate/planning/Project_Execution_Plan_v3.md

# FLOOD CNN加速器Demo部署执行计划

> **状态说明（2026-08-08）**：这是原 FLOOD CNN Demo 的六周协作计划，现作为历史资料与任务拆分参考保留。当前毕设主线及已确认的技术决策见[正式设计规格](../docs/superpowers/specs/2026-08-08-sd15-resnetblock-accelerator-design.md)，面向 6 个月以上周期的新排期见[SD1.5 ResNetBlock AXKU15 实施计划](../docs/superpowers/plans/2026-08-08-sd15-resnetblock-accelerator-implementation.md)；本文不应被误认为新项目排期。

## 一、项目概况

| 项目要素 | 内容 |
|---|---|
| 当前状态 | mac_test_tb2完成单层卷积验证，具备多层CNN框架(cnn_multilayer.c) |
| 目标 | 6人协作完成Demo部署，验证加速器通用性 |
| 硬件平台 | AKU15 FPGA + Vivado + Hybrid-SDK |
| 工具链 | RISC-V GCC (riscv64-unknown-elf-gcc) |

---

## 二、协作模式

### 2.1 总体安排

6人按周轮换任务方向，每周聚焦同一类任务。

| 周次 | 任务主题 |
|---|---|
| Week 1 | 环境熟悉 + 单层验证复现 |
| Week 2 | LeNet部署 |
| Week 3 | 工具链开发 |
| Week 4 | CIFAR-10部署 |
| Week 5 | 测试验证 |
| Week 6 | FPGA上板 + 优化 |

### 2.2 组内分工

每周6人内部按以下角色分工：

| 角色 | 人数 | 职责 |
|---|---|---|
| 核心开发 | 2人 | 代码编写 |
| 验证测试 | 2人 | 测试用例、结果验证 |
| 文档工具 | 2人 | 文档编写、工具脚本、环境支持 |

---

## 三、周计划

### Week 1：代码重构 — 模块化拆分

**目标**：将mac_test_tb2拆分为6个独立模块

**任务分配**：

| 人员 | 模块 | 文件 | 内容 |
|---|---|---|---|
| 学生1 | 底层平台 | mac_platform.h/c | 地址宏、寄存器读写、中断、延时 |
| 学生2 | DMA驱动 | mac_dma.h/c | SRAM控制、DMA传输 |
| 学生3 | 配置模块 | mac_config.h/c | Tile/NoC/FSM/全局配置 |
| 学生4 | 数据加载 | mac_data.h/c | 权重/特征图写入 |
| 学生5 | 计算执行 | mac_compute.h/c | 推理执行、输出读取 |
| 学生6 | 测试主程序 | mac_test_single.c + Makefile | main()集成、编译验证 |

**检查点**：
- [ ] 6个模块文件全部提交
- [ ] make all编译通过
- [ ] 仿真结果与原版一致

---

### Week 2：LeNet-5部署

**目标**：在加速器上运行LeNet-5，识别MNIST

**前置准备**（Week 1周末完成）：
- LeNet PyTorch模型和预训练权重
- MNIST测试图片

**任务分解**：

**核心开发组（2人）**
- 编写LeNet网络配置代码（基于cnn_multilayer.c）
- 实现多层推理流程（Conv→Pool→Conv→Pool→FC）
- 输出：lenet_demo.c + lenet_weights.h

**验证测试组（2人）**
- Python实现LeNet软件推理，作为golden reference
- 对比软硬件结果，分析误差
- 输出：lenet_golden.py + 误差分析报告

**文档工具组（2人）**
- 权重量化脚本（PyTorch→C数组）
- 图像预处理脚本（PNG→C数组）
- 输出：quantize_lenet.py + preprocess_mnist.py

**检查点**：
- [ ] LeNet-5仿真运行成功
- [ ] 正确识别至少5张MNIST图片
- [ ] 软硬件误差<5%

---

### Week 3：工具链完善

**目标**：建立PyTorch到加速器的完整工具链

**任务分解**：

**核心开发组（2人）**
- 封装通用CNN推理API（不依赖具体网络）
- 实现层配置自动生成函数
- 输出：cnn_api.c/h

**验证测试组（2人）**
- 测试工具链各环节正确性
- 建立回归测试基线
- 输出：toolchain_test.py + 测试报告

**文档工具组（2人）**
- 权重量化工具（支持任意网络）
- ONNX模型解析器（基础版）
- 输出：quantize_model.py + onnx_parser.py

**检查点**：
- [ ] 工具链能处理任意简单CNN
- [ ] 量化误差<2%
- [ ] 工具使用文档完整

---

### Week 4：CIFAR-10部署

**目标**：部署CIFAR-10分类器，验证工具链可用性

**任务分解**：

**核心开发组（2人）**
- 使用Week 3工具链自动生成CIFAR-10配置
- 调试多层网络在加速器上的运行
- 输出：cifar10_demo.c（工具链自动生成）

**验证测试组（2人）**
- 测试CIFAR-10准确率
- 分析各层耗时，找出瓶颈
- 输出：性能分析报告

**文档工具组（2人）**
- 优化预处理脚本（支持批量处理）
- 编写Demo使用文档
- 输出：batch_preprocess.py + 用户手册

**检查点**：
- [ ] CIFAR-10 Demo运行成功
- [ ] Top-1准确率>60%
- [ ] 工具链能一键生成Demo

---

### Week 5：测试验证与优化

**目标**：全面测试，修复bug，优化性能

**任务分解**：

**核心开发组（2人）**
- 优化内存访问模式，减少数据传输
- 实现乒乓缓冲优化
- 输出：优化后的推理代码

**验证测试组（2人）**
- 编写全面的单元测试
- 压力测试（边界条件、异常输入）
- 输出：完整测试套件 + 测试报告

**文档工具组（2人）**
- 整理所有文档，编写技术总结
- 准备演示Demo和PPT
- 输出：技术文档 + 演示材料

**检查点**：
- [ ] 所有测试通过
- [ ] 性能提升>20%
- [ ] 文档完整，可交付

---

### Week 6：FPGA上板验证

**目标**：在AKU15 FPGA上运行Demo

**任务分解**：

**核心开发组（2人）**
- 适配FPGA环境，解决板级问题
- 实现UART输出结果
- 输出：FPGA版本Demo

**验证测试组（2人）**
- 验证FPGA结果与仿真一致
- 测量实际运行时间
- 输出：上板测试报告

**文档工具组（2人）**
- 编写上板操作手册
- 录制演示视频
- 输出：操作手册 + 演示视频

**检查点**：
- [ ] FPGA上成功运行LeNet和CIFAR-10
- [ ] 上板操作文档完整
- [ ] 项目总结汇报完成

---

## 四、例会制度

| 项目 | 内容 |
|---|---|
| 时间 | 每周五下午 14:00-16:00 |

**议程**：
1. 成果演示（30分钟）：本周功能演示、问题与解决方案
2. 技术分享（30分钟）：关键知识点、踩坑记录
3. 下周计划（30分钟）：目标、分工、所需资源
4. 自由讨论（30分钟）：跨组协作、技术难点

---

## 五、代码管理

### 5.1 分支策略

```
main
  ├── week1/verify-single-layer
  ├── week2/lenet-deployment
  ├── week3/toolchain
  ├── week4/cifar10
  ├── week5/testing
  └── week6/fpga
```

### 5.2 提交规范

格式：`[Week X] 类型: 描述`

类型：
- feat: 新功能
- fix: 修复bug
- docs: 文档
- test: 测试
- tool: 工具脚本

示例：
```
[Week 2] feat: 添加LeNet第二层卷积配置
[Week 3] fix: 修复权重量化溢出问题
[Week 4] docs: 更新CIFAR-10部署文档
```

---

## 六、现有资源

### 6.1 已有代码

| 文件 | 用途 | 使用方式 |
|---|---|---|
| mac_test_tb2.c | 单层卷积参考 | 学习+复用配置函数 |
| cnn_multilayer.c | 多层框架 | 在此基础上扩展 |
| Makefile | 编译脚本 | 直接使用或小幅修改 |
| link.ld | 链接脚本 | 直接使用 |

### 6.2 已有工具链

- 编译器：riscv64-unknown-elf-gcc（已配置）
- 仿真：现有Verilog testbench
- SDK：Hybrid-SDK (Nuclei)

### 6.3 需开发的工具

- 权重量化脚本（Python）
- 图像预处理脚本（Python）
- 结果对比脚本（Python）

---

## 七、风险与应对

| 风险 | 可能性 | 应对策略 |
|---|---|---|
| 芯片回片有问题 | 中 | 先用FPGA验证，准备回测方案 |
| 某周任务完不成 | 中 | 灵活调整，可延后1周 |
| 6人协作冲突 | 低 | 明确分工，每日站会同步 |
| 工具链开发延期 | 中 | Week 2/4可手动准备权重 |

---

## 八、成功标准

### 8.1 最低目标（必须完成）

- [ ] Week 2: LeNet仿真通过
- [ ] Week 4: CIFAR-10仿真通过
- [ ] Week 6: FPGA上板成功

### 8.2 期望目标（努力完成）

- [ ] 工具链能一键部署新网络
- [ ] 准确率接近软件版本
- [ ] 有完整的文档和教程

### 8.3 挑战目标（力争完成）

- [ ] 部署MobileNet
- [ ] 实现动态网络切换
- [ ] 发表技术博客或论文

---

## 九、Week 1启动清单

### 9.1 环境准备

- [ ] 确认每人有Linux/WSL环境
- [ ] 安装RISC-V GCC工具链
- [ ] 配置好Vivado (FPGA开发)
- [ ] 克隆代码仓库

### 9.2 学习资料

- [ ] 阅读mac_test_tb2.c，理解单层卷积流程
- [ ] 阅读cnn_multilayer.c，理解多层框架
- [ ] 了解FLOOD加速器架构 (Config.scala)
- [ ] 学习Makefile和链接脚本

### 9.3 任务分配

| 人员 | 角色 | 任务 |
|---|---|---|
| 学生1 | 核心开发 | mac_test_tb2注释+驱动库提取 |
| 学生2 | 核心开发 | 配置函数封装 |
| 学生3 | 验证测试 | 跑通仿真，记录步骤 |
| 学生4 | 验证测试 | 验证结果正确性 |
| 学生5 | 文档工具 | 整理寄存器手册 |
| 学生6 | 文档工具 | 搭建Git仓库+目录结构 |

---

**文档版本**: v3.0  
**创建日期**: 2026-05-22  
**更新日期**: 2026-05-28  
**更新说明**: 精简表述，去除修饰性语言，改为直接、文书化风格
