Hughger/graduate/accelerator/src/python/difference_plot.png

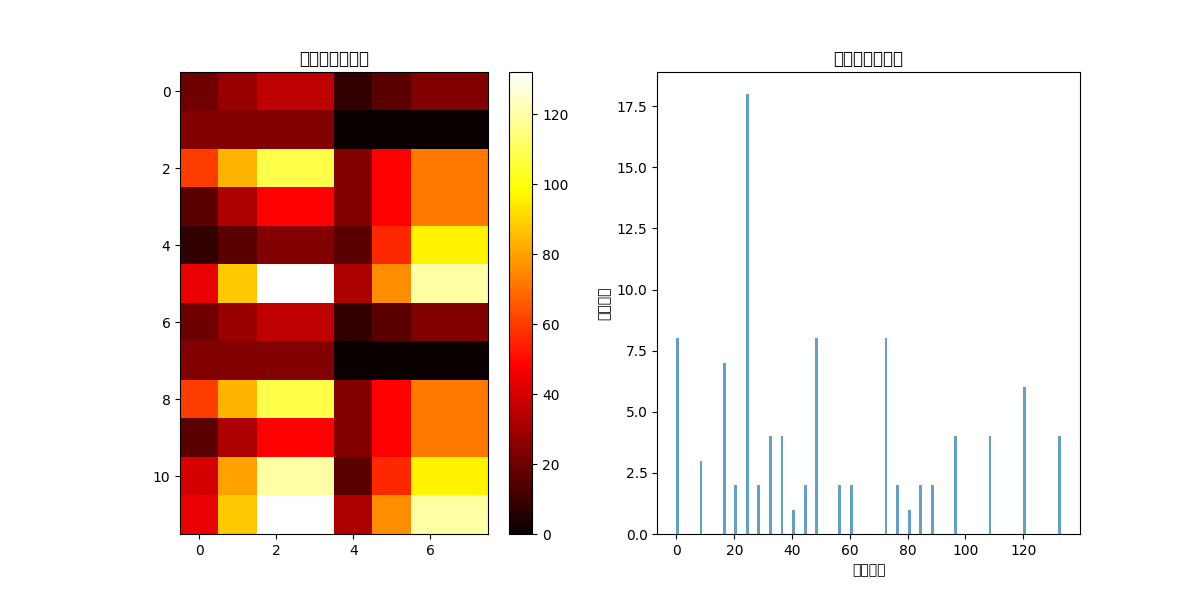
accelerator/src/python/difference_plot.png
