Hughger/graduate/accelerator/项目结构.png

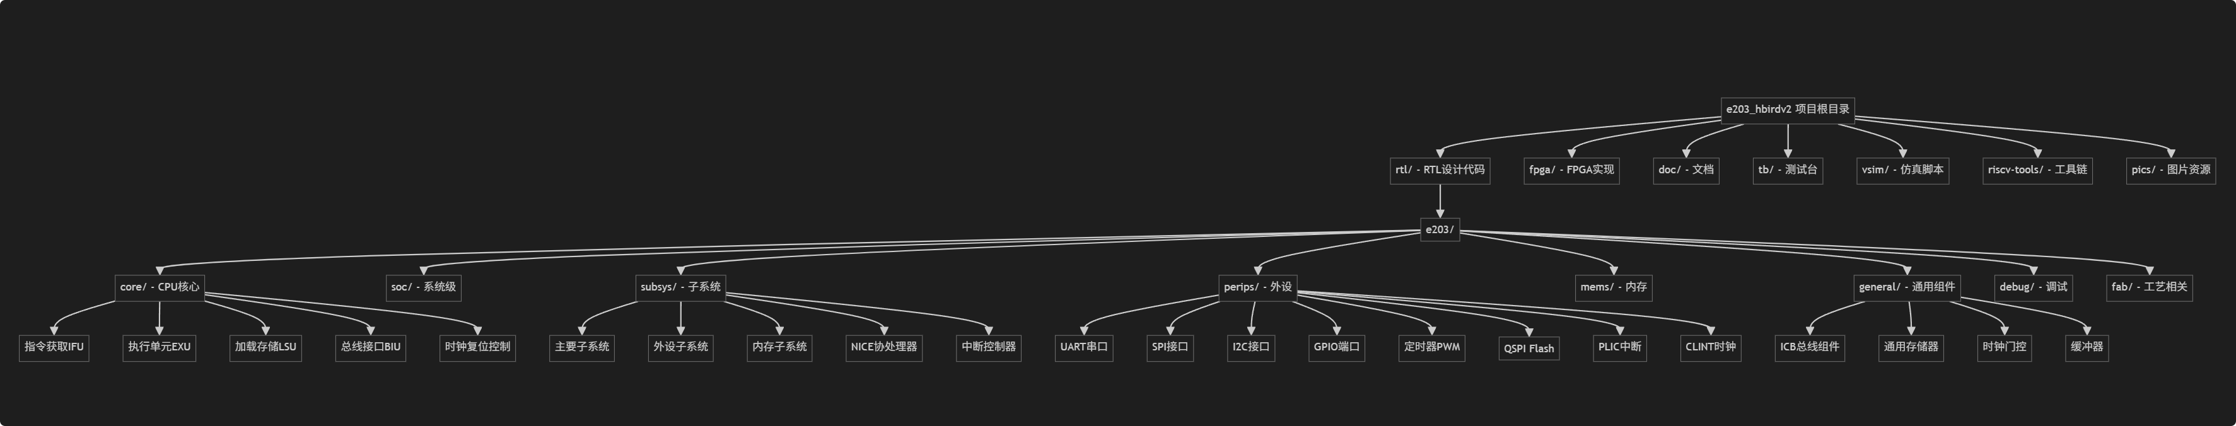
accelerator/项目结构.png
