Hughger/graduate/accelerator/docs/plans/2026-08-12-sd15-resnetblock-consecutive-transaction-verification-design.md

# SD1.5 ResNetBlock Consecutive Transaction Verification Design

**Date:** 2026-08-12  
**Status:** Implemented and simulation-validated

## Goal

Prove that the AXI64-backed fixed-point ResNetBlock prototype can complete
two distinct transactions consecutively.  The second transaction must read,
compute, and write its own data without retaining tensor, result-buffer,
DMA-address, scheduler, or response state from the first transaction.

This is a simulation-only increment.  It does not change production RTL and
does not start Vivado implementation, bitstream generation, or FPGA work.

## DUT and boundary

The DUT remains exactly:

```scala
new DiffusionAccelTop(memoryBackend = DiffusionMemoryBackend.Axi64)
```

The test reuses the current AXI64 behavioural memory, its accepted AR/AW
burst-address history, and the existing fixed-point ResNetBlock controls.  It
adds no test-only Chisel hardware and changes no file under
`accelerator/src/main`.

## Directed transactions

Each transaction processes two 512-bit vectors.  Transaction A uses the
already validated opposite-lane-order inputs at `0x400` and `0x440`, then
writes to `0x800` and `0x840`.

Transaction B uses a different pair of symmetric variance-four vectors at `0x1000` and
`0x1040`: lane 0--15 are `-2` and lane 16--31 are `+2` in the first word; the
second word reverses that order.  Its GroupNorm statistics are
`sum = 0`, `sumSquare = 256`, and `count = 64`.  It uses a different residual
vector and time embedding than transaction A, and writes to `0x1800` and
`0x1840`.

For transaction B, the reference helper is extended only as needed to support
the selected symmetric non-unit variance and its matching fixed-point rsqrt
calculation.  It must not weaken the existing variance-one reference checks.

## Required sequence and checks

1. Start transaction A, issue one two-beat read, execute GN1, Conv1, GN2,
   activation, Conv2/residual, and one two-beat write; wait for exactly one
   top-level `done` pulse.
2. Before starting transaction B, require `busy == false` and phase `Idle`.
   When B's tensor-read command is accepted, require zero tensor-buffer
   occupancy before its first DMA beat is accepted.
3. Start transaction B using a second AXI-Lite start write.  Execute the same
   phases with B's addresses, vector count, parameters, and reference values.
4. Require exactly one additional `done` pulse, then compare both transaction
   B writeback words with B's integer reference.
5. Require accepted read burst history to be
   `[0x400, 0x440, 0x1000, 0x1040]` and accepted write burst history to be
   `[0x800, 0x840, 0x1800, 0x1840]`.  Transaction A writeback words must remain
   unchanged after B completes.

Each phase output is collected only on a Decoupled handshake and compared in
vector order.  Both transactions use the staggered AW/W/B/AR/R delay profile;
all five channels must be recorded as delayed.

## Failure rules

The test fails on an absent or extra `done` pulse; non-idle state between
transactions; stale output or address history; incorrect B statistics;
misordered/missing/duplicate result; AXI protocol error; timeout; or a lane
mismatch in either transaction's writeback.

## Acceptance evidence

Required evidence is a passing focused consecutive-transaction E2E test,
passing existing single- and two-vector ResNetBlock E2E tests plus focused
AXI64/compute regressions, and successful Chisel elaboration of the unchanged
AXI64-backend top.

## Recorded evidence

On 2026-08-12, the focused buffer, E2E, AXI64, compute, and rsqrt command
listed in the companion transaction-reset design completed with 26 passing
tests in 11 suites and zero failures.  Its ResNetBlock E2E suite completed all
three directed tests: one vector, two vectors, and two consecutive
transactions.

Transaction A used opposite-lane-order `+/-1` inputs at `0x400`/`0x440`,
statistics `(sum, sumSquare, count) = (0, 64, 64)`, and writes at
`0x800`/`0x840`.  Transaction B used `+/-2` inputs at `0x1000`/`0x1040`,
statistics `(0, 256, 64)`, Q2.30 rsqrt `480191942`, distinct time/residual
values, and writes at `0x1800`/`0x1840`.

The completed test observes accepted read history
`[0x400, 0x440, 0x1000, 0x1040]`, accepted write history
`[0x800, 0x840, 0x1800, 0x1840]`, no AXI error, and all five staggered
AW/W/B/AR/R channels.  It retains a snapshot of A's two writeback words and
proves that B leaves them unchanged.  The tensor-buffer clear check occurs
after B's accepted read command and before its first payload, which is the
implemented transaction boundary.

`sbt 'runMain FLOOD_Accelerator.diffusion.GenerateDiffusionAccelAxi64TopVerilog'`
completed successfully after the focused regression.  No Vivado flow,
bitstream generation, or FPGA operation was run.
## Exclusions

This proves two directed fixed-point transactions only.  It does not establish
floating-point SD1.5 accuracy, arbitrary tensor shapes, production weights,
throughput, AXKU15 timing closure, DDR4 calibration, bitstream generation, or
FPGA programming.
