Hughger/graduate/accelerator/rtl/e203/subsys/bus/axi_x2x/src/DW_axi_x2x_xact_ctrl.v

/////////////////////////////////////////////////////////////////////////
//
// ------------------------------------------------------------------------------
// 
// Copyright 2006 - 2020 Synopsys, INC.
// 
// This Synopsys IP and all associated documentation are proprietary to
// Synopsys, Inc. and may only be used pursuant to the terms and conditions of a
// written license agreement with Synopsys, Inc. All other use, reproduction,
// modification, or distribution of the Synopsys IP or the associated
// documentation is strictly prohibited.
// 
// Component Name   : DW_axi_x2x
// Component Version: 1.08a
// Release Type     : GA
// ------------------------------------------------------------------------------

// 
// Release version :  1.08a
// File Version     :        $Revision: #11 $ 
// Revision: $Id: //dwh/DW_ocb/DW_axi_x2x/amba_dev/src/DW_axi_x2x_xact_ctrl.v#11 $ 
//
/////////////////////////////////////////////////////////////////////////

`include "DW_axi_x2x_all_includes.vh"

/////////////////////////////////////////////////////////////////////////
// xact control
/////////////////////////////////////////////////////////////////////////

module DW_axi_x2x_xact_ctrl (
  //inputs
  resize_ctrl_i,
  aready_i,
  xact_upsize_i,
  mp_total_byte_i,
  aburst_i,
  last_rs_xact_ctl_r_i,
  total_remain_bytes_i,
  deduct_ran_num_bytes_i,
  
  //outputs
  micro_ctrl_o,
  last_rs_xact_ctl_o
);

  //parameters
  parameter MAX_SP_TOTAL_BYTE = `X2X_MAX_SP_TOTAL_BYTE; //max_asize*
  parameter MAX_MP_TOTAL_BYTE = `X2X_MAX_MP_TOTAL_BYTE; //max_asize*
//  parameter INT_AW            = `X2X_INTERNAL_AW; //Internal address 
                                                  //width
//  parameter SP_BLW            = `X2X_SP_BLW;      //SP burst length width
  parameter MP_BLW            = `X2X_MP_BLW;      //MP burst length width
//  parameter LOG2_SP_SW        = `X2X_LOG2_SP_SW;  //log2^SP_SW
//  parameter MAX_SP_ASIZE      = `X2X_MAX_SP_ASIZE;//bytes -> asize
  parameter LOG2_MP_SW        = (`X2X_LOG2_MP_SW > 0) ?
                                `X2X_LOG2_MP_SW : 1;   //log2^MP_S
//  parameter LOG2_BIG_SW       = (`X2X_LOG2_MP_SW >= `X2X_LOG2_SP_SW) ?
//                                 `X2X_LOG2_MP_SW : `X2X_LOG2_SP_SW;
//  parameter LOG2_BIG_BW       = LOG2_BIG_SW + SP_BLW;//big asize + SP len
  parameter LOG2_MP_BW        = LOG2_MP_SW + MP_BLW;  //MP asize + alen;
  parameter SPBYTE_LGR_MP     = MAX_MP_TOTAL_BYTE <= MAX_SP_TOTAL_BYTE;
                                              //1 -> SP bytes larger MP


  //inputs
  input  [2:0]         resize_ctrl_i;           //resize control
  input                aready_i;                //aready
  input                xact_upsize_i;           //upsize enable
  input  [LOG2_MP_BW:0] mp_total_byte_i;        //MP total byte number
  input  [1:0]         aburst_i;                //aburst
  input                last_rs_xact_ctl_r_i;    //last xact ctrl
  input  [LOG2_MP_BW:0] total_remain_bytes_i;    //total remian fix byte
  input  [LOG2_MP_BW:0] deduct_ran_num_bytes_i; //ran byte num
  
  //outputs
  output [3:0]         micro_ctrl_o;            //micro control
  // DW_axi_x2x_xtrl module is used in both read and write channels and the signal last_rs_xact_ctl_o is only used for read channels.
  output               last_rs_xact_ctl_o;      //last RS xact ctrl

  reg  [3:0]           mux_micro_ctrl;
  reg  [3:0]           mxui_micro_ctrl;
  reg  [3:0]           mxi_micro_ctrl;
  reg                  mxui_xact_ctrl;
  reg                  mxi_xact_ctrl;
  reg                  mux_xact_ctrl;
  reg  [3:0]           micro_ctrl_o;            //micro control
  reg                  last_rs_xact_ctl_o;      //last RS xact ctrl

   
  always @( mp_total_byte_i or aready_i
            or aburst_i or total_remain_bytes_i
            or last_rs_xact_ctl_r_i
            or deduct_ran_num_bytes_i ) begin: MUX_CTRL_PROC
    mux_micro_ctrl = 4'h0;
    mux_xact_ctrl  = last_rs_xact_ctl_r_i;

     // spyglass disable_block TA_09
     // SMD: Reports cause of uncontrollability or unobservability and estimates the number of nets whose controllability / observability is impacted. 
     // SJ : Tool will issue unobservability warning only for those bits which are "not read" or "floating". Since we are not reading those bits we don't need observability. Hence waiving this warnin
        if ( aburst_i == `X2X_BT_FIXED &&
            total_remain_bytes_i > deduct_ran_num_bytes_i) begin //nolast
          mux_micro_ctrl = `MUX_FI_MUL;

          if ( aready_i )
            mux_xact_ctrl = 1'b0;
        end
        else if ( aburst_i == `X2X_BT_INCR &&
          mp_total_byte_i > deduct_ran_num_bytes_i) begin //not last xact
          mux_micro_ctrl = `MUX_FI_MUL;
  
          if ( aready_i )
            mux_xact_ctrl = 1'b0;
        end
        else begin //last xact
          mux_micro_ctrl = `MUX_FI_LAST;

          if ( aready_i )
            mux_xact_ctrl = 1'b1;
        end
    // spyglass enable_block TA_09
  end

  //if resize_ctrl_i == `MUL_XACT_INLAST
  //spyglass disable_block W415a
  //SMD: Signal may be multiply assigned (beside initialization) in the same scope.
  //SJ : mxi_micro_ctrl is initialized before assignment.
  always @( aready_i or 
            last_rs_xact_ctl_r_i ) begin:MXI_CTRL_PROC
    mxi_micro_ctrl = 4'h0;
    mxi_xact_ctrl  = last_rs_xact_ctl_r_i;

        mxi_micro_ctrl = `MXI_FI;

        if ( aready_i )
          mxi_xact_ctrl = 1'b0;
  end
  //spyglass enable_block W415a
  wire spbyte_lgr_mp;
  assign spbyte_lgr_mp = (mp_total_byte_i <= `X2X_MAX_SP_TOTAL_BYTE) |
                         SPBYTE_LGR_MP;

  //if resize_ctrl_i == `MUL_XACT_OR_US_INLAST
  always @( xact_upsize_i or 
            aready_i or spbyte_lgr_mp or
            last_rs_xact_ctl_r_i ) begin:MXUI_CTRL_PROC
    mxui_micro_ctrl = 4'h0;
    mxui_xact_ctrl  = last_rs_xact_ctl_r_i;

         // Turn off coverage for this section of code if 
         // no upsizing has been configured.
          //VCS coverage off
        if ( xact_upsize_i ) begin //upsize
          if ( spbyte_lgr_mp ) begin //SingleXact
            mxui_micro_ctrl = `MXUI_FI_SINGLE;

            if ( aready_i )
              mxui_xact_ctrl = 1'b1;
          end
          else begin //multi xact
            mxui_micro_ctrl = `MXUI_FI_MUL;

            if ( aready_i )
              mxui_xact_ctrl = 1'b0;
          end
        end
        else begin //downsize, multi xact
          //VCS coverage on 
          mxui_micro_ctrl = `MXUI_FI_DS;

          if ( aready_i )
            mxui_xact_ctrl = 1'b0;
        end
  end

  //micro_ctrl and xact_ctl mux
  always @( resize_ctrl_i or mxui_micro_ctrl or mxui_xact_ctrl or
            mux_micro_ctrl or mux_xact_ctrl or mxi_micro_ctrl or
            mxi_xact_ctrl or last_rs_xact_ctl_r_i or aready_i ) begin:LAST_RS_CTL_PROC
    last_rs_xact_ctl_o = last_rs_xact_ctl_r_i;
    micro_ctrl_o       = `IDLE_CTRL;

    case ( resize_ctrl_i )
      `AS_IS_OR_US_INLAST, `SINGLE_XACT_INLAST: begin
        if ( aready_i )
          last_rs_xact_ctl_o = 1'b1;
      end

      `MUL_XACT_OR_US_INLAST: begin
        last_rs_xact_ctl_o = mxui_xact_ctrl;
        micro_ctrl_o       = mxui_micro_ctrl;
      end 

      `MUL_XACT_INLAST: begin
        last_rs_xact_ctl_o = mxi_xact_ctrl;
        micro_ctrl_o       = mxi_micro_ctrl;
      end

      `MUL_XACT_OR_US_NOTLAST, `MUL_XACT_NOTLAST: begin
        last_rs_xact_ctl_o = mux_xact_ctrl;
        micro_ctrl_o       = mux_micro_ctrl;
      end

      default: begin
        last_rs_xact_ctl_o = last_rs_xact_ctl_r_i;
        micro_ctrl_o       = 4'h0;
      end
    endcase
  end

endmodule
