Hughger/graduate/accelerator/rtl/e203/subsys/mac_unit/tsdn28hpcpuhdb1024x128m4mwa_130a_tt0p9v25c.v

//*#*********************************************************************************************************************/
//*# Software       : TSMC MEMORY COMPILER tsn28hpcpuhddpsram_2012.02.00.d.130a						*/
//*# Technology     : TSMC 28nm CMOS LOGIC High Performance Compact Mobile 1P10M HKMG CU_ELK 0.9V				*/
//*# Memory Type    : TSMC 28nm High Performance Compact Mobile Ultra High Density Dual Port SRAM with d127 bit cell SVT Periphery */
//*# Library Name   : tsdn28hpcpuhdb1024x128m4mwa (user specify : TSDN28HPCPUHDB1024X128M4MWA)				*/
//*# Library Version: 130a												*/
//*# Generated Time : 2025/09/14, 14:20:39										*/
//*#*********************************************************************************************************************/
//*#															*/
//*# STATEMENT OF USE													*/
//*#															*/
//*# This information contains confidential and proprietary information of TSMC.					*/
//*# No part of this information may be reproduced, transmitted, transcribed,						*/
//*# stored in a retrieval system, or translated into any human or computer						*/
//*# language, in any form or by any means, electronic, mechanical, magnetic,						*/
//*# optical, chemical, manual, or otherwise, without the prior written permission					*/
//*# of TSMC. This information was prepared for informational purpose and is for					*/
//*# use by TSMC's customers only. TSMC reserves the right to make changes in the					*/
//*# information at any time and without notice.									*/
//*#															*/
//*#*********************************************************************************************************************/
///*******************************************************************************/
//*      Usage Limitation: PLEASE READ CAREFULLY FOR CORRECT USAGE               */
//* The model doesn't support the control enable, data, address signals          */
//* transition at positive clock edge.                                           */
//* Please have some timing delays between control/data/address and clock signals*/
//* to ensure the correct behavior.                                              */
//*                                                                              */
//* Please be careful when using non 2^n  memory.                                */
//* In a non-fully decoded array, a write cycle to a nonexistent address location*/
//* does not change the memory array contents and output remains the same.       */
//* In a non-fully decoded array, a read cycle to a nonexistent address location */
//* does not change the memory array contents but output becomes unknown.        */
//*                                                                              */
//* In the verilog model, the behavior of unknown clock will corrupt the         */
//* memory data and make output unknown regardless of CEB signal.  But in the    */
//* silicon, the unknown clock at CEB high, the memory and output data will be   */
//* held. The verilog model behavior is more conservative in this condition.     */
//*                                                                              */
//* The model doesn't identify physical column and row address                   */
//*                                                                              */
//* The verilog model provides TSMC_CM_UNIT_DELAY mode for the fast function     */
//* simulation.                                                                  */
//* All timing values in the specification are not checked in the                */
//* TSMC_CM_UNIT_DELAY mode simulation.                                          */
//*                                                                              */
//*                                                                              */
//*                                                                              */
//* Please use the verilog simulator version with $recrem timing check support.  */
//* Some earlier simulator versions might support $recovery only, not $recrem.   */
//*                                                                              */
//* Template Version : S_01_61101                                       */
//****************************************************************************** */
//*      Macro Usage       : (+define[MACRO] for Verilog compiliers)             */
//* +TSMC_CM_UNIT_DELAY : Enable fast function simulation.                       */
//* +no_warning : Disable all runtime warnings message from this model.          */
//* +TSMC_INITIALIZE_MEM : Initialize the memory data in verilog format.         */
//* +TSMC_INITIALIZE_FAULT : Initialize the memory fault data in verilog format. */
//* +TSMC_NO_TESTPINS_WARNING : Disable the wrong test pins connection error     */
//*                             message if necessary.                            */
//****************************************************************************** */

`resetall
`celldefine

`delay_mode_path
`suppress_faults
`enable_portfaults

module TSDN28HPCPUHDB1024X128M4MWA
    (
           RTSEL,
           WTSEL,
           PTSEL,
    AA,
    DA,
    BWEBA,
    WEBA,CEBA,CLK,
    AB,
    DB,
    BWEBB,
    WEBB,CEBB,
    AWT,
    QA,
    QB
  );

// Parameter declarations
parameter  N = 128;
parameter  W = 1024;
parameter  M = 10;
parameter  RA = 8;

    wire SLP=1'b0;
    wire DSLP=1'b0;
    wire SD=1'b0;
    input [1:0] RTSEL;
    input [1:0] WTSEL;
    input [1:0] PTSEL;

// Input-Output declarations

    input [M-1:0] AA;
    input [N-1:0] DA;
    input [N-1:0] BWEBA;

    input WEBA;
    input CEBA;
    input CLK;
    input [M-1:0] AB;
    input [N-1:0] DB;
    input [N-1:0] BWEBB;
    input WEBB;
    input CEBB;
    input AWT;
    output [N-1:0] QA;
    output [N-1:0] QB;

`ifdef no_warning
parameter MES_ALL = "OFF";
`else
parameter MES_ALL = "ON";
`endif

`ifdef TSMC_CM_UNIT_DELAY
parameter  SRAM_DELAY = 0.010;
`endif
`ifdef TSMC_INITIALIZE_MEM
parameter INITIAL_MEM_DELAY = 0.01;
`else
  `ifdef TSMC_INITIALIZE_MEM_USING_DEFAULT_TASKS
parameter INITIAL_MEM_DELAY = 0.01;
  `endif
`endif
`ifdef TSMC_INITIALIZE_FAULT
parameter INITIAL_FAULT_DELAY = 0.01;
`endif

`ifdef TSMC_INITIALIZE_MEM
parameter cdeFileInit  = "TSDN28HPCPUHDB1024X128M4MWA_initial.cde";
`endif
`ifdef TSMC_INITIALIZE_FAULT
parameter cdeFileFault = "TSDN28HPCPUHDB1024X128M4MWA_fault.cde";
`endif

// Registers
reg invalid_aslp;
reg invalid_bslp;
reg invalid_adslp;
reg invalid_bdslp;
reg invalid_sdwk_dslp;

reg [N-1:0] DAL;
reg [N-1:0] DBL;
reg [N-1:0] bDBL;
 
reg [N-1:0] BWEBAL;
reg [N-1:0] BWEBBL;
reg [N-1:0] bBWEBBL;
 
reg [M-1:0] AAL;
reg [M-1:0] ABL;
 
reg WEBAL,CEBAL;
reg WEBBL,CEBBL;
 
wire [N-1:0] QAL;
wire [N-1:0] QBL;

reg valid_testpin;


reg valid_ck,valid_cka,valid_ckb;
reg valid_cea, valid_ceb;
reg valid_wea, valid_web;
reg valid_aa;
reg valid_ab;
reg valid_contentiona,valid_contentionb,valid_contentionc;
reg valid_da127, valid_da126, valid_da125, valid_da124, valid_da123, valid_da122, valid_da121, valid_da120, valid_da119, valid_da118, valid_da117, valid_da116, valid_da115, valid_da114, valid_da113, valid_da112, valid_da111, valid_da110, valid_da109, valid_da108, valid_da107, valid_da106, valid_da105, valid_da104, valid_da103, valid_da102, valid_da101, valid_da100, valid_da99, valid_da98, valid_da97, valid_da96, valid_da95, valid_da94, valid_da93, valid_da92, valid_da91, valid_da90, valid_da89, valid_da88, valid_da87, valid_da86, valid_da85, valid_da84, valid_da83, valid_da82, valid_da81, valid_da80, valid_da79, valid_da78, valid_da77, valid_da76, valid_da75, valid_da74, valid_da73, valid_da72, valid_da71, valid_da70, valid_da69, valid_da68, valid_da67, valid_da66, valid_da65, valid_da64, valid_da63, valid_da62, valid_da61, valid_da60, valid_da59, valid_da58, valid_da57, valid_da56, valid_da55, valid_da54, valid_da53, valid_da52, valid_da51, valid_da50, valid_da49, valid_da48, valid_da47, valid_da46, valid_da45, valid_da44, valid_da43, valid_da42, valid_da41, valid_da40, valid_da39, valid_da38, valid_da37, valid_da36, valid_da35, valid_da34, valid_da33, valid_da32, valid_da31, valid_da30, valid_da29, valid_da28, valid_da27, valid_da26, valid_da25, valid_da24, valid_da23, valid_da22, valid_da21, valid_da20, valid_da19, valid_da18, valid_da17, valid_da16, valid_da15, valid_da14, valid_da13, valid_da12, valid_da11, valid_da10, valid_da9, valid_da8, valid_da7, valid_da6, valid_da5, valid_da4, valid_da3, valid_da2, valid_da1, valid_da0;
reg valid_db127, valid_db126, valid_db125, valid_db124, valid_db123, valid_db122, valid_db121, valid_db120, valid_db119, valid_db118, valid_db117, valid_db116, valid_db115, valid_db114, valid_db113, valid_db112, valid_db111, valid_db110, valid_db109, valid_db108, valid_db107, valid_db106, valid_db105, valid_db104, valid_db103, valid_db102, valid_db101, valid_db100, valid_db99, valid_db98, valid_db97, valid_db96, valid_db95, valid_db94, valid_db93, valid_db92, valid_db91, valid_db90, valid_db89, valid_db88, valid_db87, valid_db86, valid_db85, valid_db84, valid_db83, valid_db82, valid_db81, valid_db80, valid_db79, valid_db78, valid_db77, valid_db76, valid_db75, valid_db74, valid_db73, valid_db72, valid_db71, valid_db70, valid_db69, valid_db68, valid_db67, valid_db66, valid_db65, valid_db64, valid_db63, valid_db62, valid_db61, valid_db60, valid_db59, valid_db58, valid_db57, valid_db56, valid_db55, valid_db54, valid_db53, valid_db52, valid_db51, valid_db50, valid_db49, valid_db48, valid_db47, valid_db46, valid_db45, valid_db44, valid_db43, valid_db42, valid_db41, valid_db40, valid_db39, valid_db38, valid_db37, valid_db36, valid_db35, valid_db34, valid_db33, valid_db32, valid_db31, valid_db30, valid_db29, valid_db28, valid_db27, valid_db26, valid_db25, valid_db24, valid_db23, valid_db22, valid_db21, valid_db20, valid_db19, valid_db18, valid_db17, valid_db16, valid_db15, valid_db14, valid_db13, valid_db12, valid_db11, valid_db10, valid_db9, valid_db8, valid_db7, valid_db6, valid_db5, valid_db4, valid_db3, valid_db2, valid_db1, valid_db0;
reg valid_bwa127, valid_bwa126, valid_bwa125, valid_bwa124, valid_bwa123, valid_bwa122, valid_bwa121, valid_bwa120, valid_bwa119, valid_bwa118, valid_bwa117, valid_bwa116, valid_bwa115, valid_bwa114, valid_bwa113, valid_bwa112, valid_bwa111, valid_bwa110, valid_bwa109, valid_bwa108, valid_bwa107, valid_bwa106, valid_bwa105, valid_bwa104, valid_bwa103, valid_bwa102, valid_bwa101, valid_bwa100, valid_bwa99, valid_bwa98, valid_bwa97, valid_bwa96, valid_bwa95, valid_bwa94, valid_bwa93, valid_bwa92, valid_bwa91, valid_bwa90, valid_bwa89, valid_bwa88, valid_bwa87, valid_bwa86, valid_bwa85, valid_bwa84, valid_bwa83, valid_bwa82, valid_bwa81, valid_bwa80, valid_bwa79, valid_bwa78, valid_bwa77, valid_bwa76, valid_bwa75, valid_bwa74, valid_bwa73, valid_bwa72, valid_bwa71, valid_bwa70, valid_bwa69, valid_bwa68, valid_bwa67, valid_bwa66, valid_bwa65, valid_bwa64, valid_bwa63, valid_bwa62, valid_bwa61, valid_bwa60, valid_bwa59, valid_bwa58, valid_bwa57, valid_bwa56, valid_bwa55, valid_bwa54, valid_bwa53, valid_bwa52, valid_bwa51, valid_bwa50, valid_bwa49, valid_bwa48, valid_bwa47, valid_bwa46, valid_bwa45, valid_bwa44, valid_bwa43, valid_bwa42, valid_bwa41, valid_bwa40, valid_bwa39, valid_bwa38, valid_bwa37, valid_bwa36, valid_bwa35, valid_bwa34, valid_bwa33, valid_bwa32, valid_bwa31, valid_bwa30, valid_bwa29, valid_bwa28, valid_bwa27, valid_bwa26, valid_bwa25, valid_bwa24, valid_bwa23, valid_bwa22, valid_bwa21, valid_bwa20, valid_bwa19, valid_bwa18, valid_bwa17, valid_bwa16, valid_bwa15, valid_bwa14, valid_bwa13, valid_bwa12, valid_bwa11, valid_bwa10, valid_bwa9, valid_bwa8, valid_bwa7, valid_bwa6, valid_bwa5, valid_bwa4, valid_bwa3, valid_bwa2, valid_bwa1, valid_bwa0;
reg valid_bwb127, valid_bwb126, valid_bwb125, valid_bwb124, valid_bwb123, valid_bwb122, valid_bwb121, valid_bwb120, valid_bwb119, valid_bwb118, valid_bwb117, valid_bwb116, valid_bwb115, valid_bwb114, valid_bwb113, valid_bwb112, valid_bwb111, valid_bwb110, valid_bwb109, valid_bwb108, valid_bwb107, valid_bwb106, valid_bwb105, valid_bwb104, valid_bwb103, valid_bwb102, valid_bwb101, valid_bwb100, valid_bwb99, valid_bwb98, valid_bwb97, valid_bwb96, valid_bwb95, valid_bwb94, valid_bwb93, valid_bwb92, valid_bwb91, valid_bwb90, valid_bwb89, valid_bwb88, valid_bwb87, valid_bwb86, valid_bwb85, valid_bwb84, valid_bwb83, valid_bwb82, valid_bwb81, valid_bwb80, valid_bwb79, valid_bwb78, valid_bwb77, valid_bwb76, valid_bwb75, valid_bwb74, valid_bwb73, valid_bwb72, valid_bwb71, valid_bwb70, valid_bwb69, valid_bwb68, valid_bwb67, valid_bwb66, valid_bwb65, valid_bwb64, valid_bwb63, valid_bwb62, valid_bwb61, valid_bwb60, valid_bwb59, valid_bwb58, valid_bwb57, valid_bwb56, valid_bwb55, valid_bwb54, valid_bwb53, valid_bwb52, valid_bwb51, valid_bwb50, valid_bwb49, valid_bwb48, valid_bwb47, valid_bwb46, valid_bwb45, valid_bwb44, valid_bwb43, valid_bwb42, valid_bwb41, valid_bwb40, valid_bwb39, valid_bwb38, valid_bwb37, valid_bwb36, valid_bwb35, valid_bwb34, valid_bwb33, valid_bwb32, valid_bwb31, valid_bwb30, valid_bwb29, valid_bwb28, valid_bwb27, valid_bwb26, valid_bwb25, valid_bwb24, valid_bwb23, valid_bwb22, valid_bwb21, valid_bwb20, valid_bwb19, valid_bwb18, valid_bwb17, valid_bwb16, valid_bwb15, valid_bwb14, valid_bwb13, valid_bwb12, valid_bwb11, valid_bwb10, valid_bwb9, valid_bwb8, valid_bwb7, valid_bwb6, valid_bwb5, valid_bwb4, valid_bwb3, valid_bwb2, valid_bwb1, valid_bwb0;
 
reg EN;
reg RDA, RDB;

reg RCLKA,RCLKB;


wire [1:0] bRTSEL;
wire [1:0] bWTSEL;
wire [1:0] bPTSEL;


wire [N-1:0] bBWEBA;
wire [N-1:0] bBWEBB;
 
wire [N-1:0] bDA;
wire [N-1:0] bDB;
 
wire [M-1:0] bAA;
wire [M-1:0] bAB;
wire [RA-1:0] rowAA;
wire [RA-1:0] rowAB;
 
wire bWEBA,bWEBB;
wire bCEBA,bCEBB;
wire bCLKA,bCLKB;
 
reg [N-1:0] bQA;
reg [N-1:0] bQB;

wire bBIST;
wire WEA,WEB,CSA,CSB;
wire bAWT;
reg valid_awt_wk;
wire iCEBA = bCEBA;
wire iCEBB = bCEBB;
wire iCLKA = bCLKA;
wire iCLKB = bCLKB;
wire [N-1:0] iBWEBA = bBWEBA;
wire [N-1:0] iBWEBB = bBWEBB;

wire [N-1:0] bbQA;
wire [N-1:0] bbQB;
 
integer i;
integer clk_count;
integer sd_mode;




// Address Inputs
buf sAA0 (bAA[0], AA[0]);
buf sAB0 (bAB[0], AB[0]);
buf sAA1 (bAA[1], AA[1]);
buf sAB1 (bAB[1], AB[1]);
buf sAA2 (bAA[2], AA[2]);
buf sAB2 (bAB[2], AB[2]);
buf sAA3 (bAA[3], AA[3]);
buf sAB3 (bAB[3], AB[3]);
buf sAA4 (bAA[4], AA[4]);
buf sAB4 (bAB[4], AB[4]);
buf sAA5 (bAA[5], AA[5]);
buf sAB5 (bAB[5], AB[5]);
buf sAA6 (bAA[6], AA[6]);
buf sAB6 (bAB[6], AB[6]);
buf sAA7 (bAA[7], AA[7]);
buf sAB7 (bAB[7], AB[7]);
buf sAA8 (bAA[8], AA[8]);
buf sAB8 (bAB[8], AB[8]);
buf sAA9 (bAA[9], AA[9]);
buf sAB9 (bAB[9], AB[9]);
buf srAA0 (rowAA[0], AA[2]);
buf srAB0 (rowAB[0], AB[2]);
buf srAA1 (rowAA[1], AA[3]);
buf srAB1 (rowAB[1], AB[3]);
buf srAA2 (rowAA[2], AA[4]);
buf srAB2 (rowAB[2], AB[4]);
buf srAA3 (rowAA[3], AA[5]);
buf srAB3 (rowAB[3], AB[5]);
buf srAA4 (rowAA[4], AA[6]);
buf srAB4 (rowAB[4], AB[6]);
buf srAA5 (rowAA[5], AA[7]);
buf srAB5 (rowAB[5], AB[7]);
buf srAA6 (rowAA[6], AA[8]);
buf srAB6 (rowAB[6], AB[8]);
buf srAA7 (rowAA[7], AA[9]);
buf srAB7 (rowAB[7], AB[9]);


// Bit Write/Data Inputs 
buf sDA0 (bDA[0], DA[0]);
buf sDB0 (bDB[0], DB[0]);
buf sDA1 (bDA[1], DA[1]);
buf sDB1 (bDB[1], DB[1]);
buf sDA2 (bDA[2], DA[2]);
buf sDB2 (bDB[2], DB[2]);
buf sDA3 (bDA[3], DA[3]);
buf sDB3 (bDB[3], DB[3]);
buf sDA4 (bDA[4], DA[4]);
buf sDB4 (bDB[4], DB[4]);
buf sDA5 (bDA[5], DA[5]);
buf sDB5 (bDB[5], DB[5]);
buf sDA6 (bDA[6], DA[6]);
buf sDB6 (bDB[6], DB[6]);
buf sDA7 (bDA[7], DA[7]);
buf sDB7 (bDB[7], DB[7]);
buf sDA8 (bDA[8], DA[8]);
buf sDB8 (bDB[8], DB[8]);
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
buf sQB91 (QB[91], bbQB[91]);
buf sQB92 (QB[92], bbQB[92]);
buf sQB93 (QB[93], bbQB[93]);
buf sQB94 (QB[94], bbQB[94]);
buf sQB95 (QB[95], bbQB[95]);
buf sQB96 (QB[96], bbQB[96]);
buf sQB97 (QB[97], bbQB[97]);
buf sQB98 (QB[98], bbQB[98]);
buf sQB99 (QB[99], bbQB[99]);
buf sQB100 (QB[100], bbQB[100]);
buf sQB101 (QB[101], bbQB[101]);
buf sQB102 (QB[102], bbQB[102]);
buf sQB103 (QB[103], bbQB[103]);
buf sQB104 (QB[104], bbQB[104]);
buf sQB105 (QB[105], bbQB[105]);
buf sQB106 (QB[106], bbQB[106]);
buf sQB107 (QB[107], bbQB[107]);
buf sQB108 (QB[108], bbQB[108]);
buf sQB109 (QB[109], bbQB[109]);
buf sQB110 (QB[110], bbQB[110]);
buf sQB111 (QB[111], bbQB[111]);
buf sQB112 (QB[112], bbQB[112]);
buf sQB113 (QB[113], bbQB[113]);
buf sQB114 (QB[114], bbQB[114]);
buf sQB115 (QB[115], bbQB[115]);
buf sQB116 (QB[116], bbQB[116]);
buf sQB117 (QB[117], bbQB[117]);
buf sQB118 (QB[118], bbQB[118]);
buf sQB119 (QB[119], bbQB[119]);
buf sQB120 (QB[120], bbQB[120]);
buf sQB121 (QB[121], bbQB[121]);
buf sQB122 (QB[122], bbQB[122]);
buf sQB123 (QB[123], bbQB[123]);
buf sQB124 (QB[124], bbQB[124]);
buf sQB125 (QB[125], bbQB[125]);
buf sQB126 (QB[126], bbQB[126]);
buf sQB127 (QB[127], bbQB[127]);

assign bbQA=bQA;
assign bbQB=bQB;

//and sWEA (WEA, !bWEBA, !bCEBA);
//and sWEB (WEB, !bWEBB, !bCEBB);
assign WEA = !bSLP & !bDSLP & !bSD & !bCEBA & !bWEBA;
assign WEB = !bSLP & !bDSLP & !bSD & !bCEBB & !bWEBB;

//buf sCSA (CSA, !bCEBA);
//buf sCSB (CSB, !bCEBB);
assign CSA = !bSLP & !bDSLP & !bSD & !bCEBA;
assign CSB = !bSLP & !bDSLP & !bSD & !bCEBB;

wire check_noidle_b = ~CEBBL & ~bSD & ~bDSLP & ~bSLP;
wire check_idle_b = CEBBL & ~bSD & ~bDSLP & ~bSLP;
wire check_noidle_a = ~CEBAL & ~bSD & ~bDSLP & ~bSLP;
wire check_idle_a = CEBAL & ~bSD & ~bDSLP & ~bSLP;
wire check_noidle_norm_b = check_noidle_b & ~bBIST;
wire check_noidle_bist_b = check_noidle_b & bBIST;
wire check_idle_norm_b = check_idle_b & ~bBIST;
wire check_idle_bist_b = check_idle_b & bBIST;
wire check_noidle_norm_a = check_noidle_a & ~bBIST;
wire check_noidle_bist_a = check_noidle_a & bBIST;
wire check_idle_norm_a = check_idle_a & !bBIST;
wire check_idle_bist_a = check_idle_a & bBIST;

wire check_ceb  = (~iCEBA | ~iCEBB) & ~bSD & ~bDSLP & ~bSLP;
wire check_ceba = ~iCEBA & ~bSD & ~bDSLP & ~bSLP;
wire check_cebb = ~iCEBB & ~bSD & ~bDSLP & ~bSLP;
wire check_cebm = (~iCEBA | ~iCEBB) & ~bSD & ~bDSLP & ~bSLP;
wire check_ceb_a  = ~iCEBA & iCEBB & ~bSD & ~bDSLP & ~bSLP;
wire check_ceb_b  = iCEBA & ~iCEBB & ~bSD & ~bDSLP & ~bSLP;
wire check_ceb_ab = ~iCEBA & ~iCEBB & ~bSD & ~bDSLP & ~bSLP;





wire check_slp = !bSD & !bDSLP;
wire check_dslp = !bSD & !bSLP;


`ifdef TSMC_CM_UNIT_DELAY
`else
specify
    specparam PATHPULSE$ = ( 0, 0.001 );

specparam
tckl = 0.1069200,
tckh = 0.1069200,
tcyc  = 0.9104550,


taas = 0.0666989,
taah = 0.0702311,
tdas = 0.0100000,
tdah = 0.1024367,
tcas = 0.0943211,
tcah = 0.0874400,
twas = 0.0928300,
twah = 0.0695100,
tbwas = 0.0108067,
tbwah = 0.1021067,

tabs = 0.0100000,
tabh = 0.0874400,
tdbs = 0.0100000,
tdbh = 0.1436133,
tcbs = 0.0943211,
tcbh = 0.0874400,
twbs = 0.0100000,
twbh = 0.0874400,
tbwbs = 0.0100000,
tbwbh = 0.1435644,

ttests = 0.910,
ttesth = 0.910,
tawtq = 0.2819672,
tawtqh = 0.1280572,
tdq = 0.1541511,
tdqh = 0.0810050,
tbwebq = 0.1499089,
tbwebqh = 0.0872100,
tcda   = 0.4568364,
tcdb   = 0.9102217,
`ifdef TSMC_CM_READ_X_SQUASHING
tholda    = 0.4568364,
tholdb    = 0.9102217;
`else
tholda    = 0.3140372,
tholdb    = 0.6868472;
`endif

    $setuphold (posedge CLK &&& check_noidle_a, posedge RTSEL[0], ttests, 0, valid_testpin); 
    $setuphold (posedge CLK &&& check_noidle_a, negedge RTSEL[0], ttests, 0, valid_testpin);
    $setuphold (posedge CLK &&& check_idle_a, posedge RTSEL[0], 0, ttesth, valid_testpin); 
    $setuphold (posedge CLK &&& check_idle_a, negedge RTSEL[0], 0, ttesth, valid_testpin);
    $setuphold (posedge CLK &&& check_noidle_a, posedge RTSEL[1], ttests, 0, valid_testpin); 
    $setuphold (posedge CLK &&& check_noidle_a, negedge RTSEL[1], ttests, 0, valid_testpin);
    $setuphold (posedge CLK &&& check_idle_a, posedge RTSEL[1], 0, ttesth, valid_testpin); 
    $setuphold (posedge CLK &&& check_idle_a, negedge RTSEL[1], 0, ttesth, valid_testpin);
    $setuphold (posedge CLK &&& check_noidle_a, posedge WTSEL[0], ttests, 0, valid_testpin); 
    $setuphold (posedge CLK &&& check_noidle_a, negedge WTSEL[0], ttests, 0, valid_testpin);
    $setuphold (posedge CLK &&& check_idle_a, posedge WTSEL[0], 0, ttesth, valid_testpin); 
    $setuphold (posedge CLK &&& check_idle_a, negedge WTSEL[0], 0, ttesth, valid_testpin);
    $setuphold (posedge CLK &&& check_noidle_a, posedge WTSEL[1], ttests, 0, valid_testpin); 
    $setuphold (posedge CLK &&& check_noidle_a, negedge WTSEL[1], ttests, 0, valid_testpin);
    $setuphold (posedge CLK &&& check_idle_a, posedge WTSEL[1], 0, ttesth, valid_testpin); 
    $setuphold (posedge CLK &&& check_idle_a, negedge WTSEL[1], 0, ttesth, valid_testpin);
    $setuphold (posedge CLK &&& check_noidle_a, posedge PTSEL[0], ttests, 0, valid_testpin); 
    $setuphold (posedge CLK &&& check_noidle_a, negedge PTSEL[0], ttests, 0, valid_testpin);
    $setuphold (posedge CLK &&& check_idle_a, posedge PTSEL[0], 0, ttesth, valid_testpin); 
    $setuphold (posedge CLK &&& check_idle_a, negedge PTSEL[0], 0, ttesth, valid_testpin);
    $setuphold (posedge CLK &&& check_noidle_a, posedge PTSEL[1], ttests, 0, valid_testpin); 
    $setuphold (posedge CLK &&& check_noidle_a, negedge PTSEL[1], ttests, 0, valid_testpin);
    $setuphold (posedge CLK &&& check_idle_a, posedge PTSEL[1], 0, ttesth, valid_testpin); 
    $setuphold (posedge CLK &&& check_idle_a, negedge PTSEL[1], 0, ttesth, valid_testpin);
    $setuphold (posedge CLK &&& check_noidle_b, posedge RTSEL[0], ttests, 0, valid_testpin); 
    $setuphold (posedge CLK &&& check_noidle_b, negedge RTSEL[0], ttests, 0, valid_testpin);
    $setuphold (posedge CLK &&& check_idle_b, posedge RTSEL[0], 0, ttesth, valid_testpin); 
    $setuphold (posedge CLK &&& check_idle_b, negedge RTSEL[0], 0, ttesth, valid_testpin);
    $setuphold (posedge CLK &&& check_noidle_b, posedge RTSEL[1], ttests, 0, valid_testpin); 
    $setuphold (posedge CLK &&& check_noidle_b, negedge RTSEL[1], ttests, 0, valid_testpin);
    $setuphold (posedge CLK &&& check_idle_b, posedge RTSEL[1], 0, ttesth, valid_testpin); 
    $setuphold (posedge CLK &&& check_idle_b, negedge RTSEL[1], 0, ttesth, valid_testpin);
    $setuphold (posedge CLK &&& check_noidle_b, posedge WTSEL[0], ttests, 0, valid_testpin); 
    $setuphold (posedge CLK &&& check_noidle_b, negedge WTSEL[0], ttests, 0, valid_testpin);
    $setuphold (posedge CLK &&& check_idle_b, posedge WTSEL[0], 0, ttesth, valid_testpin); 
    $setuphold (posedge CLK &&& check_idle_b, negedge WTSEL[0], 0, ttesth, valid_testpin);
    $setuphold (posedge CLK &&& check_noidle_b, posedge WTSEL[1], ttests, 0, valid_testpin); 
    $setuphold (posedge CLK &&& check_noidle_b, negedge WTSEL[1], ttests, 0, valid_testpin);
    $setuphold (posedge CLK &&& check_idle_b, posedge WTSEL[1], 0, ttesth, valid_testpin); 
    $setuphold (posedge CLK &&& check_idle_b, negedge WTSEL[1], 0, ttesth, valid_testpin);
    $setuphold (posedge CLK &&& check_noidle_b, posedge PTSEL[0], ttests, 0, valid_testpin); 
    $setuphold (posedge CLK &&& check_noidle_b, negedge PTSEL[0], ttests, 0, valid_testpin);
    $setuphold (posedge CLK &&& check_idle_b, posedge PTSEL[0], 0, ttesth, valid_testpin); 
    $setuphold (posedge CLK &&& check_idle_b, negedge PTSEL[0], 0, ttesth, valid_testpin);
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
    $setuphold (posedge CLK &&& WEB, posedge BWEBB[103], tbwbs, tbwbh, valid_bwb103);
    $setuphold (posedge CLK &&& WEB, negedge BWEBB[103], tbwbs, tbwbh, valid_bwb103);
    $setuphold (posedge CLK &&& WEA, posedge DA[104], tdas, tdah, valid_da104);
    $setuphold (posedge CLK &&& WEA, negedge DA[104], tdas, tdah, valid_da104);
    $setuphold (posedge CLK &&& WEB, posedge DB[104], tdbs, tdbh, valid_db104);
    $setuphold (posedge CLK &&& WEB, negedge DB[104], tdbs, tdbh, valid_db104);
 
    $setuphold (posedge CLK &&& WEA, posedge BWEBA[104], tbwas, tbwah, valid_bwa104);
    $setuphold (posedge CLK &&& WEA, negedge BWEBA[104], tbwas, tbwah, valid_bwa104);
    $setuphold (posedge CLK &&& WEB, posedge BWEBB[104], tbwbs, tbwbh, valid_bwb104);
    $setuphold (posedge CLK &&& WEB, negedge BWEBB[104], tbwbs, tbwbh, valid_bwb104);
    $setuphold (posedge CLK &&& WEA, posedge DA[105], tdas, tdah, valid_da105);
    $setuphold (posedge CLK &&& WEA, negedge DA[105], tdas, tdah, valid_da105);
    $setuphold (posedge CLK &&& WEB, posedge DB[105], tdbs, tdbh, valid_db105);
    $setuphold (posedge CLK &&& WEB, negedge DB[105], tdbs, tdbh, valid_db105);
 
    $setuphold (posedge CLK &&& WEA, posedge BWEBA[105], tbwas, tbwah, valid_bwa105);
    $setuphold (posedge CLK &&& WEA, negedge BWEBA[105], tbwas, tbwah, valid_bwa105);
    $setuphold (posedge CLK &&& WEB, posedge BWEBB[105], tbwbs, tbwbh, valid_bwb105);
    $setuphold (posedge CLK &&& WEB, negedge BWEBB[105], tbwbs, tbwbh, valid_bwb105);
    $setuphold (posedge CLK &&& WEA, posedge DA[106], tdas, tdah, valid_da106);
    $setuphold (posedge CLK &&& WEA, negedge DA[106], tdas, tdah, valid_da106);
    $setuphold (posedge CLK &&& WEB, posedge DB[106], tdbs, tdbh, valid_db106);
    $setuphold (posedge CLK &&& WEB, negedge DB[106], tdbs, tdbh, valid_db106);
 
    $setuphold (posedge CLK &&& WEA, posedge BWEBA[106], tbwas, tbwah, valid_bwa106);
    $setuphold (posedge CLK &&& WEA, negedge BWEBA[106], tbwas, tbwah, valid_bwa106);
    $setuphold (posedge CLK &&& WEB, posedge BWEBB[106], tbwbs, tbwbh, valid_bwb106);
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
