Hughger/graduate/accelerator/rtl/e203/subsys/bus/axi_matrix/src/DW_axi-undef.v

   `undef ACT_ID_BUF_POINTER_W_AR_M1
   `undef ACT_ID_BUF_POINTER_W_AR_M10
   `undef ACT_ID_BUF_POINTER_W_AR_M11
   `undef ACT_ID_BUF_POINTER_W_AR_M12
   `undef ACT_ID_BUF_POINTER_W_AR_M13
   `undef ACT_ID_BUF_POINTER_W_AR_M14
   `undef ACT_ID_BUF_POINTER_W_AR_M15
   `undef ACT_ID_BUF_POINTER_W_AR_M16
   `undef ACT_ID_BUF_POINTER_W_AR_M2
   `undef ACT_ID_BUF_POINTER_W_AR_M3
   `undef ACT_ID_BUF_POINTER_W_AR_M4
   `undef ACT_ID_BUF_POINTER_W_AR_M5
   `undef ACT_ID_BUF_POINTER_W_AR_M6
   `undef ACT_ID_BUF_POINTER_W_AR_M7
   `undef ACT_ID_BUF_POINTER_W_AR_M8
   `undef ACT_ID_BUF_POINTER_W_AR_M9
   `undef ACT_ID_BUF_POINTER_W_AW_M1
   `undef ACT_ID_BUF_POINTER_W_AW_M10
   `undef ACT_ID_BUF_POINTER_W_AW_M11
   `undef ACT_ID_BUF_POINTER_W_AW_M12
   `undef ACT_ID_BUF_POINTER_W_AW_M13
   `undef ACT_ID_BUF_POINTER_W_AW_M14
   `undef ACT_ID_BUF_POINTER_W_AW_M15
   `undef ACT_ID_BUF_POINTER_W_AW_M16
   `undef ACT_ID_BUF_POINTER_W_AW_M2
   `undef ACT_ID_BUF_POINTER_W_AW_M3
   `undef ACT_ID_BUF_POINTER_W_AW_M4
   `undef ACT_ID_BUF_POINTER_W_AW_M5
   `undef ACT_ID_BUF_POINTER_W_AW_M6
   `undef ACT_ID_BUF_POINTER_W_AW_M7
   `undef ACT_ID_BUF_POINTER_W_AW_M8
   `undef ACT_ID_BUF_POINTER_W_AW_M9
   `undef APB_ADDR_WIDTH
   `undef APB_DATA_WIDTH
   `undef ARB_OP_MODE_NOREG
   `undef ARB_PARK_INDEX
   `undef ARB_PRIOR_W
   `undef AXI_4
   `undef AXI_ACC_NON_LCL_SLV_S1
   `undef AXI_ACC_NON_LCL_SLV_S10
   `undef AXI_ACC_NON_LCL_SLV_S11
   `undef AXI_ACC_NON_LCL_SLV_S12
   `undef AXI_ACC_NON_LCL_SLV_S13
   `undef AXI_ACC_NON_LCL_SLV_S14
   `undef AXI_ACC_NON_LCL_SLV_S15
   `undef AXI_ACC_NON_LCL_SLV_S16
   `undef AXI_ACC_NON_LCL_SLV_S2
   `undef AXI_ACC_NON_LCL_SLV_S3
   `undef AXI_ACC_NON_LCL_SLV_S4
   `undef AXI_ACC_NON_LCL_SLV_S5
   `undef AXI_ACC_NON_LCL_SLV_S6
   `undef AXI_ACC_NON_LCL_SLV_S7
   `undef AXI_ACC_NON_LCL_SLV_S8
   `undef AXI_ACC_NON_LCL_SLV_S9
   `undef AXI_ACELITE
   `undef AXI_ADDR_CH
   `undef AXI_ALBW
   `undef AXI_ALDW
   `undef AXI_ALLOW_MST1_ICM1
   `undef AXI_ALLOW_MST1_ICM2
   `undef AXI_ALLOW_MST1_ICM3
   `undef AXI_ALLOW_MST1_ICM4
   `undef AXI_ALLOW_MST2_ICM1
   `undef AXI_ALLOW_MST2_ICM2
   `undef AXI_ALLOW_MST2_ICM3
   `undef AXI_ALLOW_MST2_ICM4
   `undef AXI_ALLOW_MST3_ICM1
   `undef AXI_ALLOW_MST3_ICM2
   `undef AXI_ALLOW_MST3_ICM3
   `undef AXI_ALLOW_MST3_ICM4
   `undef AXI_ALLOW_MST4_ICM1
   `undef AXI_ALLOW_MST4_ICM2
   `undef AXI_ALLOW_MST4_ICM3
   `undef AXI_ALLOW_MST4_ICM4
   `undef AXI_ALLOW_MST5_ICM1
   `undef AXI_ALLOW_MST5_ICM2
   `undef AXI_ALLOW_MST5_ICM3
   `undef AXI_ALLOW_MST5_ICM4
   `undef AXI_ALLOW_MST6_ICM1
   `undef AXI_ALLOW_MST6_ICM2
   `undef AXI_ALLOW_MST6_ICM3
   `undef AXI_ALLOW_MST6_ICM4
   `undef AXI_ALLOW_MST7_ICM1
   `undef AXI_ALLOW_MST7_ICM2
   `undef AXI_ALLOW_MST7_ICM3
   `undef AXI_ALLOW_MST7_ICM4
   `undef AXI_ALLOW_MST8_ICM1
   `undef AXI_ALLOW_MST8_ICM2
   `undef AXI_ALLOW_MST8_ICM3
   `undef AXI_ALLOW_MST8_ICM4
   `undef AXI_ALL_AR_LAYER_SHARED
   `undef AXI_ALL_AW_LAYER_SHARED
   `undef AXI_ALL_B_LAYER_SHARED
   `undef AXI_ALL_R_LAYER_SHARED
   `undef AXI_ALL_W_LAYER_SHARED
   `undef AXI_ALSW
   `undef AXI_ARB_TYPE_2T
   `undef AXI_ARB_TYPE_DP
   `undef AXI_ARB_TYPE_FCFS
   `undef AXI_ARB_TYPE_QOS
   `undef AXI_ARB_TYPE_USER
   `undef AXI_ARPYLD_ADDR
   `undef AXI_ARPYLD_ADDR_LHS
   `undef AXI_ARPYLD_ADDR_RHS
   `undef AXI_ARPYLD_BURST
   `undef AXI_ARPYLD_BURST_LHS
   `undef AXI_ARPYLD_BURST_RHS
   `undef AXI_ARPYLD_CACHE
   `undef AXI_ARPYLD_CACHE_LHS
   `undef AXI_ARPYLD_CACHE_RHS
   `undef AXI_ARPYLD_ID_LHS_M
   `undef AXI_ARPYLD_ID_LHS_S
   `undef AXI_ARPYLD_ID_M
   `undef AXI_ARPYLD_ID_RHS_M
   `undef AXI_ARPYLD_ID_RHS_S
   `undef AXI_ARPYLD_ID_S
   `undef AXI_ARPYLD_LEN
   `undef AXI_ARPYLD_LEN_LHS
   `undef AXI_ARPYLD_LEN_RHS
   `undef AXI_ARPYLD_LOCK
   `undef AXI_ARPYLD_LOCK_LHS
   `undef AXI_ARPYLD_LOCK_RHS
   `undef AXI_ARPYLD_PROT
   `undef AXI_ARPYLD_PROT_LHS
   `undef AXI_ARPYLD_PROT_RHS
   `undef AXI_ARPYLD_SIZE
   `undef AXI_ARPYLD_SIZE_LHS
   `undef AXI_ARPYLD_SIZE_RHS
   `undef AXI_ARQOS_INT_M1
   `undef AXI_ARQOS_INT_M2
   `undef AXI_ARQOS_INT_M3
   `undef AXI_AR_ARB_TYPE_S0
   `undef AXI_AR_ARB_TYPE_S1
   `undef AXI_AR_ARB_TYPE_S10
   `undef AXI_AR_ARB_TYPE_S11
   `undef AXI_AR_ARB_TYPE_S12
   `undef AXI_AR_ARB_TYPE_S13
   `undef AXI_AR_ARB_TYPE_S14
   `undef AXI_AR_ARB_TYPE_S15
   `undef AXI_AR_ARB_TYPE_S16
   `undef AXI_AR_ARB_TYPE_S2
   `undef AXI_AR_ARB_TYPE_S3
   `undef AXI_AR_ARB_TYPE_S4
   `undef AXI_AR_ARB_TYPE_S5
   `undef AXI_AR_ARB_TYPE_S6
   `undef AXI_AR_ARB_TYPE_S7
   `undef AXI_AR_ARB_TYPE_S8
   `undef AXI_AR_ARB_TYPE_S9
   `undef AXI_AR_HAS_QOS_REGULATOR_M1
   `undef AXI_AR_HAS_QOS_REGULATOR_M10
   `undef AXI_AR_HAS_QOS_REGULATOR_M11
   `undef AXI_AR_HAS_QOS_REGULATOR_M12
   `undef AXI_AR_HAS_QOS_REGULATOR_M13
   `undef AXI_AR_HAS_QOS_REGULATOR_M14
   `undef AXI_AR_HAS_QOS_REGULATOR_M15
   `undef AXI_AR_HAS_QOS_REGULATOR_M16
   `undef AXI_AR_HAS_QOS_REGULATOR_M2
   `undef AXI_AR_HAS_QOS_REGULATOR_M3
   `undef AXI_AR_HAS_QOS_REGULATOR_M4
   `undef AXI_AR_HAS_QOS_REGULATOR_M5
   `undef AXI_AR_HAS_QOS_REGULATOR_M6
   `undef AXI_AR_HAS_QOS_REGULATOR_M7
   `undef AXI_AR_HAS_QOS_REGULATOR_M8
   `undef AXI_AR_HAS_QOS_REGULATOR_M9
   `undef AXI_AR_HAS_SHARED_LAYER
   `undef AXI_AR_LAYER_S0_M1
   `undef AXI_AR_LAYER_S0_M10
   `undef AXI_AR_LAYER_S0_M11
   `undef AXI_AR_LAYER_S0_M12
   `undef AXI_AR_LAYER_S0_M13
   `undef AXI_AR_LAYER_S0_M14
   `undef AXI_AR_LAYER_S0_M15
   `undef AXI_AR_LAYER_S0_M16
   `undef AXI_AR_LAYER_S0_M2
   `undef AXI_AR_LAYER_S0_M3
   `undef AXI_AR_LAYER_S0_M4
   `undef AXI_AR_LAYER_S0_M5
   `undef AXI_AR_LAYER_S0_M6
   `undef AXI_AR_LAYER_S0_M7
   `undef AXI_AR_LAYER_S0_M8
   `undef AXI_AR_LAYER_S0_M9
   `undef AXI_AR_LAYER_S10_M1
   `undef AXI_AR_LAYER_S10_M10
   `undef AXI_AR_LAYER_S10_M11
   `undef AXI_AR_LAYER_S10_M12
   `undef AXI_AR_LAYER_S10_M13
   `undef AXI_AR_LAYER_S10_M14
   `undef AXI_AR_LAYER_S10_M15
   `undef AXI_AR_LAYER_S10_M16
   `undef AXI_AR_LAYER_S10_M2
   `undef AXI_AR_LAYER_S10_M3
   `undef AXI_AR_LAYER_S10_M4
   `undef AXI_AR_LAYER_S10_M5
   `undef AXI_AR_LAYER_S10_M6
   `undef AXI_AR_LAYER_S10_M7
   `undef AXI_AR_LAYER_S10_M8
   `undef AXI_AR_LAYER_S10_M9
   `undef AXI_AR_LAYER_S11_M1
   `undef AXI_AR_LAYER_S11_M10
   `undef AXI_AR_LAYER_S11_M11
   `undef AXI_AR_LAYER_S11_M12
   `undef AXI_AR_LAYER_S11_M13
   `undef AXI_AR_LAYER_S11_M14
   `undef AXI_AR_LAYER_S11_M15
   `undef AXI_AR_LAYER_S11_M16
   `undef AXI_AR_LAYER_S11_M2
   `undef AXI_AR_LAYER_S11_M3
   `undef AXI_AR_LAYER_S11_M4
   `undef AXI_AR_LAYER_S11_M5
   `undef AXI_AR_LAYER_S11_M6
   `undef AXI_AR_LAYER_S11_M7
   `undef AXI_AR_LAYER_S11_M8
   `undef AXI_AR_LAYER_S11_M9
   `undef AXI_AR_LAYER_S12_M1
   `undef AXI_AR_LAYER_S12_M10
   `undef AXI_AR_LAYER_S12_M11
   `undef AXI_AR_LAYER_S12_M12
   `undef AXI_AR_LAYER_S12_M13
   `undef AXI_AR_LAYER_S12_M14
   `undef AXI_AR_LAYER_S12_M15
   `undef AXI_AR_LAYER_S12_M16
   `undef AXI_AR_LAYER_S12_M2
   `undef AXI_AR_LAYER_S12_M3
   `undef AXI_AR_LAYER_S12_M4
   `undef AXI_AR_LAYER_S12_M5
   `undef AXI_AR_LAYER_S12_M6
   `undef AXI_AR_LAYER_S12_M7
   `undef AXI_AR_LAYER_S12_M8
   `undef AXI_AR_LAYER_S12_M9
   `undef AXI_AR_LAYER_S13_M1
   `undef AXI_AR_LAYER_S13_M10
   `undef AXI_AR_LAYER_S13_M11
   `undef AXI_AR_LAYER_S13_M12
   `undef AXI_AR_LAYER_S13_M13
   `undef AXI_AR_LAYER_S13_M14
   `undef AXI_AR_LAYER_S13_M15
   `undef AXI_AR_LAYER_S13_M16
   `undef AXI_AR_LAYER_S13_M2
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
   `undef AXI_AR_MCA_NC_W_S4
   `undef AXI_AR_MCA_NC_W_S5
   `undef AXI_AR_MCA_NC_W_S6
   `undef AXI_AR_MCA_NC_W_S7
   `undef AXI_AR_MCA_NC_W_S8
   `undef AXI_AR_MCA_NC_W_S9
   `undef AXI_AR_PL_ARB
   `undef AXI_AR_PYLD_M_W
   `undef AXI_AR_PYLD_S_W
   `undef AXI_AR_S0_HAS_SHRD_DDCTD_LNK_VAL
   `undef AXI_AR_S0_NMV
   `undef AXI_AR_S0_NMV_LOG2
   `undef AXI_AR_S0_NMV_P1_LOG2
   `undef AXI_AR_S10_HAS_SHRD_DDCTD_LNK_VAL
   `undef AXI_AR_S10_NMV
   `undef AXI_AR_S10_NMV_LOG2
   `undef AXI_AR_S10_NMV_P1_LOG2
   `undef AXI_AR_S11_HAS_SHRD_DDCTD_LNK_VAL
   `undef AXI_AR_S11_NMV
   `undef AXI_AR_S11_NMV_LOG2
   `undef AXI_AR_S11_NMV_P1_LOG2
   `undef AXI_AR_S12_HAS_SHRD_DDCTD_LNK_VAL
   `undef AXI_AR_S12_NMV
   `undef AXI_AR_S12_NMV_LOG2
   `undef AXI_AR_S12_NMV_P1_LOG2
   `undef AXI_AR_S13_HAS_SHRD_DDCTD_LNK_VAL
   `undef AXI_AR_S13_NMV
   `undef AXI_AR_S13_NMV_LOG2
   `undef AXI_AR_S13_NMV_P1_LOG2
   `undef AXI_AR_S14_HAS_SHRD_DDCTD_LNK_VAL
   `undef AXI_AR_S14_NMV
   `undef AXI_AR_S14_NMV_LOG2
   `undef AXI_AR_S14_NMV_P1_LOG2
   `undef AXI_AR_S15_HAS_SHRD_DDCTD_LNK_VAL
   `undef AXI_AR_S15_NMV
   `undef AXI_AR_S15_NMV_LOG2
   `undef AXI_AR_S15_NMV_P1_LOG2
   `undef AXI_AR_S16_HAS_SHRD_DDCTD_LNK_VAL
   `undef AXI_AR_S16_NMV
   `undef AXI_AR_S16_NMV_LOG2
   `undef AXI_AR_S16_NMV_P1_LOG2
   `undef AXI_AR_S1_HAS_SHRD_DDCTD_LNK_VAL
   `undef AXI_AR_S1_NMV
   `undef AXI_AR_S1_NMV_LOG2
   `undef AXI_AR_S1_NMV_P1_LOG2
   `undef AXI_AR_S2_HAS_SHRD_DDCTD_LNK_VAL
   `undef AXI_AR_S2_NMV
   `undef AXI_AR_S2_NMV_LOG2
   `undef AXI_AR_S2_NMV_P1_LOG2
   `undef AXI_AR_S3_HAS_SHRD_DDCTD_LNK_VAL
   `undef AXI_AR_S3_NMV
   `undef AXI_AR_S3_NMV_LOG2
   `undef AXI_AR_S3_NMV_P1_LOG2
   `undef AXI_AR_S4_HAS_SHRD_DDCTD_LNK_VAL
   `undef AXI_AR_S4_NMV
   `undef AXI_AR_S4_NMV_LOG2
   `undef AXI_AR_S4_NMV_P1_LOG2
   `undef AXI_AR_S5_HAS_SHRD_DDCTD_LNK_VAL
   `undef AXI_AR_S5_NMV
   `undef AXI_AR_S5_NMV_LOG2
   `undef AXI_AR_S5_NMV_P1_LOG2
   `undef AXI_AR_S6_HAS_SHRD_DDCTD_LNK_VAL
   `undef AXI_AR_S6_NMV
   `undef AXI_AR_S6_NMV_LOG2
   `undef AXI_AR_S6_NMV_P1_LOG2
   `undef AXI_AR_S7_HAS_SHRD_DDCTD_LNK_VAL
   `undef AXI_AR_S7_NMV
   `undef AXI_AR_S7_NMV_LOG2
   `undef AXI_AR_S7_NMV_P1_LOG2
   `undef AXI_AR_S8_HAS_SHRD_DDCTD_LNK_VAL
   `undef AXI_AR_S8_NMV
   `undef AXI_AR_S8_NMV_LOG2
   `undef AXI_AR_S8_NMV_P1_LOG2
   `undef AXI_AR_S9_HAS_SHRD_DDCTD_LNK_VAL
   `undef AXI_AR_S9_NMV
   `undef AXI_AR_S9_NMV_LOG2
   `undef AXI_AR_S9_NMV_P1_LOG2
   `undef AXI_AR_SBW
   `undef AXI_AR_SHARED_ARB_TYPE
   `undef AXI_AR_SHARED_LAYER_NM
   `undef AXI_AR_SHARED_LAYER_NS
   `undef AXI_AR_SHARED_LAYER_NS_R0
   `undef AXI_AR_SHARED_MCA_EN
   `undef AXI_AR_SHARED_MCA_NC
   `undef AXI_AR_SHARED_MCA_NC_W
   `undef AXI_AR_SHARED_PL
   `undef AXI_AR_TMO
   `undef AXI_AW
   `undef AXI_AWPYLD_ADDR
   `undef AXI_AWPYLD_ADDR_LHS
   `undef AXI_AWPYLD_ADDR_RHS
   `undef AXI_AWPYLD_BURST
   `undef AXI_AWPYLD_BURST_LHS
   `undef AXI_AWPYLD_BURST_RHS
   `undef AXI_AWPYLD_CACHE
   `undef AXI_AWPYLD_CACHE_LHS
   `undef AXI_AWPYLD_CACHE_RHS
   `undef AXI_AWPYLD_ID_LHS_M
   `undef AXI_AWPYLD_ID_LHS_S
   `undef AXI_AWPYLD_ID_M
   `undef AXI_AWPYLD_ID_RHS_M
   `undef AXI_AWPYLD_ID_RHS_S
   `undef AXI_AWPYLD_ID_S
   `undef AXI_AWPYLD_LEN
   `undef AXI_AWPYLD_LEN_LHS
   `undef AXI_AWPYLD_LEN_RHS
   `undef AXI_AWPYLD_LOCK
   `undef AXI_AWPYLD_LOCK_LHS
   `undef AXI_AWPYLD_LOCK_RHS
   `undef AXI_AWPYLD_PROT
   `undef AXI_AWPYLD_PROT_LHS
   `undef AXI_AWPYLD_PROT_RHS
   `undef AXI_AWPYLD_SIZE
   `undef AXI_AWPYLD_SIZE_LHS
   `undef AXI_AWPYLD_SIZE_RHS
   `undef AXI_AWQOS_INT_M1
   `undef AXI_AWQOS_INT_M2
   `undef AXI_AWQOS_INT_M3
   `undef AXI_AW_ARB_TYPE_S0
   `undef AXI_AW_ARB_TYPE_S1
   `undef AXI_AW_ARB_TYPE_S10
   `undef AXI_AW_ARB_TYPE_S11
   `undef AXI_AW_ARB_TYPE_S12
   `undef AXI_AW_ARB_TYPE_S13
   `undef AXI_AW_ARB_TYPE_S14
   `undef AXI_AW_ARB_TYPE_S15
   `undef AXI_AW_ARB_TYPE_S16
   `undef AXI_AW_ARB_TYPE_S2
   `undef AXI_AW_ARB_TYPE_S3
   `undef AXI_AW_ARB_TYPE_S4
   `undef AXI_AW_ARB_TYPE_S5
   `undef AXI_AW_ARB_TYPE_S6
   `undef AXI_AW_ARB_TYPE_S7
   `undef AXI_AW_ARB_TYPE_S8
   `undef AXI_AW_ARB_TYPE_S9
   `undef AXI_AW_CH
   `undef AXI_AW_HAS_QOS_REGULATOR_M1
   `undef AXI_AW_HAS_QOS_REGULATOR_M10
   `undef AXI_AW_HAS_QOS_REGULATOR_M11
   `undef AXI_AW_HAS_QOS_REGULATOR_M12
   `undef AXI_AW_HAS_QOS_REGULATOR_M13
   `undef AXI_AW_HAS_QOS_REGULATOR_M14
   `undef AXI_AW_HAS_QOS_REGULATOR_M15
   `undef AXI_AW_HAS_QOS_REGULATOR_M16
   `undef AXI_AW_HAS_QOS_REGULATOR_M2
   `undef AXI_AW_HAS_QOS_REGULATOR_M3
   `undef AXI_AW_HAS_QOS_REGULATOR_M4
   `undef AXI_AW_HAS_QOS_REGULATOR_M5
   `undef AXI_AW_HAS_QOS_REGULATOR_M6
   `undef AXI_AW_HAS_QOS_REGULATOR_M7
   `undef AXI_AW_HAS_QOS_REGULATOR_M8
   `undef AXI_AW_HAS_QOS_REGULATOR_M9
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
   `undef AXI_AW_S12_NMV_P1_LOG2
   `undef AXI_AW_S13_HAS_SHRD_DDCTD_LNK_VAL
   `undef AXI_AW_S13_NMV
   `undef AXI_AW_S13_NMV_LOG2
   `undef AXI_AW_S13_NMV_P1_LOG2
   `undef AXI_AW_S14_HAS_SHRD_DDCTD_LNK_VAL
   `undef AXI_AW_S14_NMV
   `undef AXI_AW_S14_NMV_LOG2
   `undef AXI_AW_S14_NMV_P1_LOG2
   `undef AXI_AW_S15_HAS_SHRD_DDCTD_LNK_VAL
   `undef AXI_AW_S15_NMV
   `undef AXI_AW_S15_NMV_LOG2
   `undef AXI_AW_S15_NMV_P1_LOG2
   `undef AXI_AW_S16_HAS_SHRD_DDCTD_LNK_VAL
   `undef AXI_AW_S16_NMV
   `undef AXI_AW_S16_NMV_LOG2
   `undef AXI_AW_S16_NMV_P1_LOG2
   `undef AXI_AW_S1_HAS_SHRD_DDCTD_LNK_VAL
   `undef AXI_AW_S1_NMV
   `undef AXI_AW_S1_NMV_LOG2
   `undef AXI_AW_S1_NMV_P1_LOG2
   `undef AXI_AW_S2_HAS_SHRD_DDCTD_LNK_VAL
   `undef AXI_AW_S2_NMV
   `undef AXI_AW_S2_NMV_LOG2
   `undef AXI_AW_S2_NMV_P1_LOG2
   `undef AXI_AW_S3_HAS_SHRD_DDCTD_LNK_VAL
   `undef AXI_AW_S3_NMV
   `undef AXI_AW_S3_NMV_LOG2
   `undef AXI_AW_S3_NMV_P1_LOG2
   `undef AXI_AW_S4_HAS_SHRD_DDCTD_LNK_VAL
   `undef AXI_AW_S4_NMV
   `undef AXI_AW_S4_NMV_LOG2
   `undef AXI_AW_S4_NMV_P1_LOG2
   `undef AXI_AW_S5_HAS_SHRD_DDCTD_LNK_VAL
   `undef AXI_AW_S5_NMV
   `undef AXI_AW_S5_NMV_LOG2
   `undef AXI_AW_S5_NMV_P1_LOG2
   `undef AXI_AW_S6_HAS_SHRD_DDCTD_LNK_VAL
   `undef AXI_AW_S6_NMV
   `undef AXI_AW_S6_NMV_LOG2
   `undef AXI_AW_S6_NMV_P1_LOG2
   `undef AXI_AW_S7_HAS_SHRD_DDCTD_LNK_VAL
   `undef AXI_AW_S7_NMV
   `undef AXI_AW_S7_NMV_LOG2
   `undef AXI_AW_S7_NMV_P1_LOG2
   `undef AXI_AW_S8_HAS_SHRD_DDCTD_LNK_VAL
   `undef AXI_AW_S8_NMV
   `undef AXI_AW_S8_NMV_LOG2
   `undef AXI_AW_S8_NMV_P1_LOG2
   `undef AXI_AW_S9_HAS_SHRD_DDCTD_LNK_VAL
   `undef AXI_AW_S9_NMV
   `undef AXI_AW_S9_NMV_LOG2
   `undef AXI_AW_S9_NMV_P1_LOG2
   `undef AXI_AW_SBW
   `undef AXI_AW_SHARED_ARB_TYPE
   `undef AXI_AW_SHARED_LAYER_NM
   `undef AXI_AW_SHARED_LAYER_NS
   `undef AXI_AW_SHARED_LAYER_NS_R0
   `undef AXI_AW_SHARED_MCA_EN
   `undef AXI_AW_SHARED_MCA_NC
   `undef AXI_AW_SHARED_MCA_NC_W
   `undef AXI_AW_SHARED_PL
   `undef AXI_AW_TMO
   `undef AXI_BCM_CDC_INIT
   `undef AXI_BCM_TST_MODE
   `undef AXI_BLW
   `undef AXI_BNMV_S1
   `undef AXI_BNMV_S10
   `undef AXI_BNMV_S11
   `undef AXI_BNMV_S12
   `undef AXI_BNMV_S13
   `undef AXI_BNMV_S14
   `undef AXI_BNMV_S15
   `undef AXI_BNMV_S16
   `undef AXI_BNMV_S2
   `undef AXI_BNMV_S3
   `undef AXI_BNMV_S4
   `undef AXI_BNMV_S5
   `undef AXI_BNMV_S6
   `undef AXI_BNMV_S7
   `undef AXI_BNMV_S8
   `undef AXI_BNMV_S9
   `undef AXI_BPYLD_ID_LHS_M
   `undef AXI_BPYLD_ID_LHS_S
   `undef AXI_BPYLD_ID_M
   `undef AXI_BPYLD_ID_RHS_M
   `undef AXI_BPYLD_ID_RHS_S
   `undef AXI_BPYLD_ID_S
   `undef AXI_BPYLD_RESP
   `undef AXI_BPYLD_RESP_LHS
   `undef AXI_BPYLD_RESP_RHS
   `undef AXI_BRW
   `undef AXI_BSW
   `undef AXI_BTW
   `undef AXI_BV_S0_BY_M1
   `undef AXI_BV_S0_BY_M10
   `undef AXI_BV_S0_BY_M11
   `undef AXI_BV_S0_BY_M12
   `undef AXI_BV_S0_BY_M13
   `undef AXI_BV_S0_BY_M14
   `undef AXI_BV_S0_BY_M15
   `undef AXI_BV_S0_BY_M16
   `undef AXI_BV_S0_BY_M2
   `undef AXI_BV_S0_BY_M3
   `undef AXI_BV_S0_BY_M4
   `undef AXI_BV_S0_BY_M5
   `undef AXI_BV_S0_BY_M6
   `undef AXI_BV_S0_BY_M7
   `undef AXI_BV_S0_BY_M8
   `undef AXI_BV_S0_BY_M9
   `undef AXI_BV_S10_BY_ANY_M
   `undef AXI_BV_S10_BY_M1
   `undef AXI_BV_S10_BY_M10
   `undef AXI_BV_S10_BY_M11
   `undef AXI_BV_S10_BY_M12
   `undef AXI_BV_S10_BY_M13
   `undef AXI_BV_S10_BY_M14
   `undef AXI_BV_S10_BY_M15
   `undef AXI_BV_S10_BY_M16
   `undef AXI_BV_S10_BY_M2
   `undef AXI_BV_S10_BY_M3
   `undef AXI_BV_S10_BY_M4
   `undef AXI_BV_S10_BY_M5
   `undef AXI_BV_S10_BY_M6
   `undef AXI_BV_S10_BY_M7
   `undef AXI_BV_S10_BY_M8
   `undef AXI_BV_S10_BY_M9
   `undef AXI_BV_S11_BY_ANY_M
   `undef AXI_BV_S11_BY_M1
   `undef AXI_BV_S11_BY_M10
   `undef AXI_BV_S11_BY_M11
   `undef AXI_BV_S11_BY_M12
   `undef AXI_BV_S11_BY_M13
   `undef AXI_BV_S11_BY_M14
   `undef AXI_BV_S11_BY_M15
   `undef AXI_BV_S11_BY_M16
   `undef AXI_BV_S11_BY_M2
   `undef AXI_BV_S11_BY_M3
   `undef AXI_BV_S11_BY_M4
   `undef AXI_BV_S11_BY_M5
   `undef AXI_BV_S11_BY_M6
   `undef AXI_BV_S11_BY_M7
   `undef AXI_BV_S11_BY_M8
   `undef AXI_BV_S11_BY_M9
   `undef AXI_BV_S12_BY_ANY_M
   `undef AXI_BV_S12_BY_M1
   `undef AXI_BV_S12_BY_M10
   `undef AXI_BV_S12_BY_M11
   `undef AXI_BV_S12_BY_M12
   `undef AXI_BV_S12_BY_M13
   `undef AXI_BV_S12_BY_M14
   `undef AXI_BV_S12_BY_M15
   `undef AXI_BV_S12_BY_M16
   `undef AXI_BV_S12_BY_M2
   `undef AXI_BV_S12_BY_M3
   `undef AXI_BV_S12_BY_M4
   `undef AXI_BV_S12_BY_M5
   `undef AXI_BV_S12_BY_M6
   `undef AXI_BV_S12_BY_M7
   `undef AXI_BV_S12_BY_M8
   `undef AXI_BV_S12_BY_M9
   `undef AXI_BV_S13_BY_ANY_M
   `undef AXI_BV_S13_BY_M1
   `undef AXI_BV_S13_BY_M10
   `undef AXI_BV_S13_BY_M11
   `undef AXI_BV_S13_BY_M12
   `undef AXI_BV_S13_BY_M13
   `undef AXI_BV_S13_BY_M14
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
   `undef AXI_B_MCA_EN_M10
   `undef AXI_B_MCA_EN_M11
   `undef AXI_B_MCA_EN_M12
   `undef AXI_B_MCA_EN_M13
   `undef AXI_B_MCA_EN_M14
   `undef AXI_B_MCA_EN_M15
   `undef AXI_B_MCA_EN_M16
   `undef AXI_B_MCA_EN_M2
   `undef AXI_B_MCA_EN_M3
   `undef AXI_B_MCA_EN_M4
   `undef AXI_B_MCA_EN_M5
   `undef AXI_B_MCA_EN_M6
   `undef AXI_B_MCA_EN_M7
   `undef AXI_B_MCA_EN_M8
   `undef AXI_B_MCA_EN_M9
   `undef AXI_B_MCA_NC_M1
   `undef AXI_B_MCA_NC_M10
   `undef AXI_B_MCA_NC_M11
   `undef AXI_B_MCA_NC_M12
   `undef AXI_B_MCA_NC_M13
   `undef AXI_B_MCA_NC_M14
   `undef AXI_B_MCA_NC_M15
   `undef AXI_B_MCA_NC_M16
   `undef AXI_B_MCA_NC_M2
   `undef AXI_B_MCA_NC_M3
   `undef AXI_B_MCA_NC_M4
   `undef AXI_B_MCA_NC_M5
   `undef AXI_B_MCA_NC_M6
   `undef AXI_B_MCA_NC_M7
   `undef AXI_B_MCA_NC_M8
   `undef AXI_B_MCA_NC_M9
   `undef AXI_B_MCA_NC_W_M1
   `undef AXI_B_MCA_NC_W_M10
   `undef AXI_B_MCA_NC_W_M11
   `undef AXI_B_MCA_NC_W_M12
   `undef AXI_B_MCA_NC_W_M13
   `undef AXI_B_MCA_NC_W_M14
   `undef AXI_B_MCA_NC_W_M15
   `undef AXI_B_MCA_NC_W_M16
   `undef AXI_B_MCA_NC_W_M2
   `undef AXI_B_MCA_NC_W_M3
   `undef AXI_B_MCA_NC_W_M4
   `undef AXI_B_MCA_NC_W_M5
   `undef AXI_B_MCA_NC_W_M6
   `undef AXI_B_MCA_NC_W_M7
   `undef AXI_B_MCA_NC_W_M8
   `undef AXI_B_MCA_NC_W_M9
   `undef AXI_B_PL_ARB
   `undef AXI_B_PYLD_M_W
   `undef AXI_B_PYLD_S_W
   `undef AXI_B_SBW
   `undef AXI_B_SHARED_ARB_TYPE
   `undef AXI_B_SHARED_LAYER_NM
   `undef AXI_B_SHARED_LAYER_NM_R0
   `undef AXI_B_SHARED_LAYER_NS
   `undef AXI_B_SHARED_MCA_EN
   `undef AXI_B_SHARED_MCA_NC
   `undef AXI_B_SHARED_MCA_NC_W
   `undef AXI_B_SHARED_PL
   `undef AXI_B_TMO
   `undef AXI_CTW
   `undef AXI_DLOCK_NOTIFY_EN
   `undef AXI_DLOCK_TIMEOUT
   `undef AXI_DW
   `undef AXI_EN_MULTI_TILE_DLOCK_AVOID
   `undef AXI_HAS_APB
   `undef AXI_HAS_APB3
   `undef AXI_HAS_ARQOS_EXT_M1
   `undef AXI_HAS_ARQOS_EXT_M10
   `undef AXI_HAS_ARQOS_EXT_M11
   `undef AXI_HAS_ARQOS_EXT_M12
   `undef AXI_HAS_ARQOS_EXT_M13
   `undef AXI_HAS_ARQOS_EXT_M14
   `undef AXI_HAS_ARQOS_EXT_M15
   `undef AXI_HAS_ARQOS_EXT_M16
   `undef AXI_HAS_ARQOS_EXT_M2
   `undef AXI_HAS_ARQOS_EXT_M3
   `undef AXI_HAS_ARQOS_EXT_M4
   `undef AXI_HAS_ARQOS_EXT_M5
   `undef AXI_HAS_ARQOS_EXT_M6
   `undef AXI_HAS_ARQOS_EXT_M7
   `undef AXI_HAS_ARQOS_EXT_M8
   `undef AXI_HAS_ARQOS_EXT_M9
   `undef AXI_HAS_ARSB
   `undef AXI_HAS_AWQOS_EXT_M1
   `undef AXI_HAS_AWQOS_EXT_M10
   `undef AXI_HAS_AWQOS_EXT_M11
   `undef AXI_HAS_AWQOS_EXT_M12
   `undef AXI_HAS_AWQOS_EXT_M13
   `undef AXI_HAS_AWQOS_EXT_M14
   `undef AXI_HAS_AWQOS_EXT_M15
   `undef AXI_HAS_AWQOS_EXT_M16
   `undef AXI_HAS_AWQOS_EXT_M2
   `undef AXI_HAS_AWQOS_EXT_M3
   `undef AXI_HAS_AWQOS_EXT_M4
   `undef AXI_HAS_AWQOS_EXT_M5
   `undef AXI_HAS_AWQOS_EXT_M6
   `undef AXI_HAS_AWQOS_EXT_M7
   `undef AXI_HAS_AWQOS_EXT_M8
   `undef AXI_HAS_AWQOS_EXT_M9
   `undef AXI_HAS_AWSB
   `undef AXI_HAS_AXI4
   `undef AXI_HAS_BICMD
   `undef AXI_HAS_BSB
   `undef AXI_HAS_EXT_PRIORITY
   `undef AXI_HAS_LEGAL_ADDR_OVRLP_VAL
   `undef AXI_HAS_LOCKING
   `undef AXI_HAS_QOS
   `undef AXI_HAS_REGIONS
   `undef AXI_HAS_REGIONS_S1
   `undef AXI_HAS_REGIONS_S10
   `undef AXI_HAS_REGIONS_S11
   `undef AXI_HAS_REGIONS_S12
   `undef AXI_HAS_REGIONS_S13
   `undef AXI_HAS_REGIONS_S14
   `undef AXI_HAS_REGIONS_S15
   `undef AXI_HAS_REGIONS_S16
   `undef AXI_HAS_REGIONS_S2
   `undef AXI_HAS_REGIONS_S3
   `undef AXI_HAS_REGIONS_S4
   `undef AXI_HAS_REGIONS_S5
   `undef AXI_HAS_REGIONS_S6
   `undef AXI_HAS_REGIONS_S7
   `undef AXI_HAS_REGIONS_S8
   `undef AXI_HAS_REGIONS_S9
   `undef AXI_HAS_RSB
   `undef AXI_HAS_TZ_SUPPORT
   `undef AXI_HAS_WSB
   `undef AXI_HAS_XDCDR
   `undef AXI_HOLD_VLD_OTHER_M_W
   `undef AXI_HOLD_VLD_OTHER_S_W
   `undef AXI_IC_REG_BASE_ADDR
   `undef AXI_IDW_M1
   `undef AXI_IDW_M2
   `undef AXI_IDW_M3
   `undef AXI_IDW_M4
   `undef AXI_INITIAL_LOCKDOWN
   `undef AXI_INTERFACE_TYPE
   `undef AXI_IS_ICM_M1
   `undef AXI_IS_ICM_M10
   `undef AXI_IS_ICM_M11
   `undef AXI_IS_ICM_M12
   `undef AXI_IS_ICM_M13
   `undef AXI_IS_ICM_M14
   `undef AXI_IS_ICM_M15
   `undef AXI_IS_ICM_M16
   `undef AXI_IS_ICM_M2
   `undef AXI_IS_ICM_M3
   `undef AXI_IS_ICM_M4
   `undef AXI_IS_ICM_M5
   `undef AXI_IS_ICM_M6
   `undef AXI_IS_ICM_M7
   `undef AXI_IS_ICM_M8
   `undef AXI_IS_ICM_M9
   `undef AXI_LOG2_AR_SHARED_LAYER_NM
   `undef AXI_LOG2_AR_SHARED_LAYER_NMP1
   `undef AXI_LOG2_AR_SHARED_LAYER_NS
   `undef AXI_LOG2_AR_SHARED_LAYER_NSP1
   `undef AXI_LOG2_AW_SHARED_LAYER_NM
   `undef AXI_LOG2_AW_SHARED_LAYER_NMP1
   `undef AXI_LOG2_AW_SHARED_LAYER_NS
   `undef AXI_LOG2_AW_SHARED_LAYER_NSP1
   `undef AXI_LOG2_B_SHARED_LAYER_NM
   `undef AXI_LOG2_B_SHARED_LAYER_NMP1
   `undef AXI_LOG2_B_SHARED_LAYER_NS
   `undef AXI_LOG2_B_SHARED_LAYER_NSP1
   `undef AXI_LOG2_DLOCK_TIMEOUT_P1
   `undef AXI_LOG2_LCL_NM
   `undef AXI_LOG2_LCL_NMP1
   `undef AXI_LOG2_LOWPWR_NOPX_CNT
   `undef AXI_LOG2_MAX_FARC_P1_S0
   `undef AXI_LOG2_MAX_FARC_P1_S1
   `undef AXI_LOG2_MAX_FARC_P1_S10
   `undef AXI_LOG2_MAX_FARC_P1_S11
   `undef AXI_LOG2_MAX_FARC_P1_S12
   `undef AXI_LOG2_MAX_FARC_P1_S13
   `undef AXI_LOG2_MAX_FARC_P1_S14
   `undef AXI_LOG2_MAX_FARC_P1_S15
   `undef AXI_LOG2_MAX_FARC_P1_S16
   `undef AXI_LOG2_MAX_FARC_P1_S2
   `undef AXI_LOG2_MAX_FARC_P1_S3
   `undef AXI_LOG2_MAX_FARC_P1_S4
   `undef AXI_LOG2_MAX_FARC_P1_S5
   `undef AXI_LOG2_MAX_FARC_P1_S6
   `undef AXI_LOG2_MAX_FARC_P1_S7
   `undef AXI_LOG2_MAX_FARC_P1_S8
   `undef AXI_LOG2_MAX_FARC_P1_S9
   `undef AXI_LOG2_MAX_FAWC_P1_S0
   `undef AXI_LOG2_MAX_FAWC_P1_S1
   `undef AXI_LOG2_MAX_FAWC_P1_S10
   `undef AXI_LOG2_MAX_FAWC_P1_S11
   `undef AXI_LOG2_MAX_FAWC_P1_S12
   `undef AXI_LOG2_MAX_FAWC_P1_S13
   `undef AXI_LOG2_MAX_FAWC_P1_S14
   `undef AXI_LOG2_MAX_FAWC_P1_S15
   `undef AXI_LOG2_MAX_FAWC_P1_S16
   `undef AXI_LOG2_MAX_FAWC_P1_S2
   `undef AXI_LOG2_MAX_FAWC_P1_S3
   `undef AXI_LOG2_MAX_FAWC_P1_S4
   `undef AXI_LOG2_MAX_FAWC_P1_S5
   `undef AXI_LOG2_MAX_FAWC_P1_S6
   `undef AXI_LOG2_MAX_FAWC_P1_S7
   `undef AXI_LOG2_MAX_FAWC_P1_S8
   `undef AXI_LOG2_MAX_FAWC_P1_S9
   `undef AXI_LOG2_MAX_FAWC_S0
   `undef AXI_LOG2_MAX_FAWC_S1
   `undef AXI_LOG2_MAX_FAWC_S10
   `undef AXI_LOG2_MAX_FAWC_S11
   `undef AXI_LOG2_MAX_FAWC_S12
   `undef AXI_LOG2_MAX_FAWC_S13
   `undef AXI_LOG2_MAX_FAWC_S14
   `undef AXI_LOG2_MAX_FAWC_S15
   `undef AXI_LOG2_MAX_FAWC_S16
   `undef AXI_LOG2_MAX_FAWC_S2
   `undef AXI_LOG2_MAX_FAWC_S3
   `undef AXI_LOG2_MAX_FAWC_S4
   `undef AXI_LOG2_MAX_FAWC_S5
   `undef AXI_LOG2_MAX_FAWC_S6
   `undef AXI_LOG2_MAX_FAWC_S7
   `undef AXI_LOG2_MAX_FAWC_S8
   `undef AXI_LOG2_MAX_FAWC_S9
   `undef AXI_LOG2_MAX_RCA_ID_P1_M1
   `undef AXI_LOG2_MAX_RCA_ID_P1_M10
   `undef AXI_LOG2_MAX_RCA_ID_P1_M11
   `undef AXI_LOG2_MAX_RCA_ID_P1_M12
   `undef AXI_LOG2_MAX_RCA_ID_P1_M13
   `undef AXI_LOG2_MAX_RCA_ID_P1_M14
   `undef AXI_LOG2_MAX_RCA_ID_P1_M15
   `undef AXI_LOG2_MAX_RCA_ID_P1_M16
   `undef AXI_LOG2_MAX_RCA_ID_P1_M2
   `undef AXI_LOG2_MAX_RCA_ID_P1_M3
   `undef AXI_LOG2_MAX_RCA_ID_P1_M4
   `undef AXI_LOG2_MAX_RCA_ID_P1_M5
   `undef AXI_LOG2_MAX_RCA_ID_P1_M6
   `undef AXI_LOG2_MAX_RCA_ID_P1_M7
   `undef AXI_LOG2_MAX_RCA_ID_P1_M8
   `undef AXI_LOG2_MAX_RCA_ID_P1_M9
   `undef AXI_LOG2_MAX_URIDA_M1
   `undef AXI_LOG2_MAX_URIDA_M10
   `undef AXI_LOG2_MAX_URIDA_M11
   `undef AXI_LOG2_MAX_URIDA_M12
   `undef AXI_LOG2_MAX_URIDA_M13
   `undef AXI_LOG2_MAX_URIDA_M14
   `undef AXI_LOG2_MAX_URIDA_M15
   `undef AXI_LOG2_MAX_URIDA_M16
   `undef AXI_LOG2_MAX_URIDA_M2
   `undef AXI_LOG2_MAX_URIDA_M3
   `undef AXI_LOG2_MAX_URIDA_M4
   `undef AXI_LOG2_MAX_URIDA_M5
   `undef AXI_LOG2_MAX_URIDA_M6
   `undef AXI_LOG2_MAX_URIDA_M7
   `undef AXI_LOG2_MAX_URIDA_M8
   `undef AXI_LOG2_MAX_URIDA_M9
   `undef AXI_LOG2_MAX_UWIDA_M1
   `undef AXI_LOG2_MAX_UWIDA_M10
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
   `undef AXI_MAX_FAWC_S9
   `undef AXI_MAX_NUM_MST_SLVS
   `undef AXI_MAX_NUM_USR_MSTS
   `undef AXI_MAX_NUM_USR_SLVS
   `undef AXI_MAX_RCA_ID_M1
   `undef AXI_MAX_RCA_ID_M10
   `undef AXI_MAX_RCA_ID_M11
   `undef AXI_MAX_RCA_ID_M12
   `undef AXI_MAX_RCA_ID_M13
   `undef AXI_MAX_RCA_ID_M14
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
